EMDCYY/FFTusingFPGA/IMG_1619.jpeg

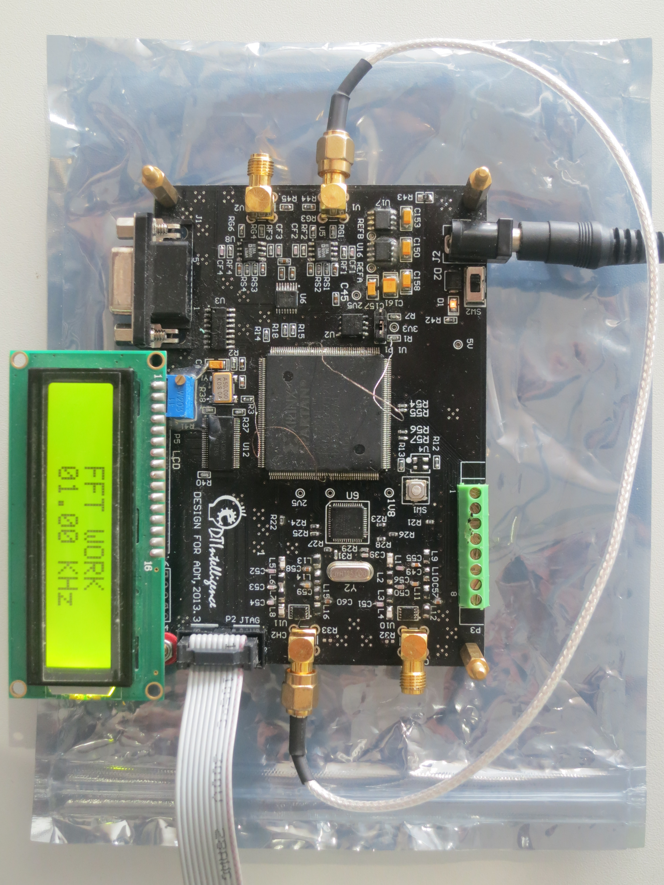
IMG_1619.jpeg
