EMDCYY/FFTusingFPGA/code/ipcore_dir/AAD.v

////////////////////////////////////////////////////////////////////////////////
// Copyright (c) 1995-2011 Xilinx, Inc.  All rights reserved.
////////////////////////////////////////////////////////////////////////////////
//   ____  ____
//  /   /\/   /
// /___/  \  /    Vendor: Xilinx
// \   \   \/     Version: O.40d
//  \   \         Application: netgen
//  /   /         Filename: AAD.v
// /___/   /\     Timestamp: Thu Aug 15 16:29:15 2013
// \   \  /  \ 
//  \___\/\___\
//             
// Command	: -w -sim -ofmt verilog "E:/Design of Laser Tracer/8.ADM/ADMDSP_CODE/ADM3.0/ipcore_dir/tmp/_cg/AAD.ngc" "E:/Design of Laser Tracer/8.ADM/ADMDSP_CODE/ADM3.0/ipcore_dir/tmp/_cg/AAD.v" 
// Device	: 3s500epq208-4
// Input file	: E:/Design of Laser Tracer/8.ADM/ADMDSP_CODE/ADM3.0/ipcore_dir/tmp/_cg/AAD.ngc
// Output file	: E:/Design of Laser Tracer/8.ADM/ADMDSP_CODE/ADM3.0/ipcore_dir/tmp/_cg/AAD.v
// # of Modules	: 1
// Design Name	: AAD
// Xilinx        : c:\Xilinx\13.1\ISE_DS\ISE\
//             
// Purpose:    
//     This verilog netlist is a verification model and uses simulation 
//     primitives which may not represent the true implementation of the 
//     device, however the netlist is functionally correct and should not 
//     be modified. This file cannot be synthesized and should only be used 
//     with supported simulation tools.
//             
// Reference:  
//     Command Line Tools User Guide, Chapter 23 and Synthesis and Simulation Design Guide, Chapter 6
//             
////////////////////////////////////////////////////////////////////////////////

`timescale 1 ns/1 ps

module AAD (
  clk, s, a, b
)/* synthesis syn_black_box syn_noprune=1 */;
  input clk;
  output [23 : 0] s;
  input [23 : 0] a;
  input [23 : 0] b;
  
  // synthesis translate_off
  
  wire N0;
  wire [22 : 0] \U0/xst_addsub/i_baseblox.i_baseblox_addsub/no_pipelining.the_addsub/i_lut4.i_lut4_addsub/carry_simple ;
  wire [23 : 0] \U0/xst_addsub/i_baseblox.i_baseblox_addsub/no_pipelining.the_addsub/i_lut4.i_lut4_addsub/halfsum ;
  wire [24 : 1] \U0/xst_addsub/i_baseblox.i_baseblox_addsub/no_pipelining.the_addsub/i_lut4.i_lut4_addsub/i_q.i_simple.qreg/fd/output ;
  wire [23 : 0] \U0/xst_addsub/i_baseblox.i_baseblox_addsub/no_pipelining.the_addsub/i_lut4.i_lut4_addsub/sum_simple ;
  assign
    s[23] = \U0/xst_addsub/i_baseblox.i_baseblox_addsub/no_pipelining.the_addsub/i_lut4.i_lut4_addsub/i_q.i_simple.qreg/fd/output [24],
    s[22] = \U0/xst_addsub/i_baseblox.i_baseblox_addsub/no_pipelining.the_addsub/i_lut4.i_lut4_addsub/i_q.i_simple.qreg/fd/output [23],
    s[21] = \U0/xst_addsub/i_baseblox.i_baseblox_addsub/no_pipelining.the_addsub/i_lut4.i_lut4_addsub/i_q.i_simple.qreg/fd/output [22],
    s[20] = \U0/xst_addsub/i_baseblox.i_baseblox_addsub/no_pipelining.the_addsub/i_lut4.i_lut4_addsub/i_q.i_simple.qreg/fd/output [21],
    s[19] = \U0/xst_addsub/i_baseblox.i_baseblox_addsub/no_pipelining.the_addsub/i_lut4.i_lut4_addsub/i_q.i_simple.qreg/fd/output [20],
    s[18] = \U0/xst_addsub/i_baseblox.i_baseblox_addsub/no_pipelining.the_addsub/i_lut4.i_lut4_addsub/i_q.i_simple.qreg/fd/output [19],
    s[17] = \U0/xst_addsub/i_baseblox.i_baseblox_addsub/no_pipelining.the_addsub/i_lut4.i_lut4_addsub/i_q.i_simple.qreg/fd/output [18],
    s[16] = \U0/xst_addsub/i_baseblox.i_baseblox_addsub/no_pipelining.the_addsub/i_lut4.i_lut4_addsub/i_q.i_simple.qreg/fd/output [17],
    s[15] = \U0/xst_addsub/i_baseblox.i_baseblox_addsub/no_pipelining.the_addsub/i_lut4.i_lut4_addsub/i_q.i_simple.qreg/fd/output [16],
    s[14] = \U0/xst_addsub/i_baseblox.i_baseblox_addsub/no_pipelining.the_addsub/i_lut4.i_lut4_addsub/i_q.i_simple.qreg/fd/output [15],
    s[13] = \U0/xst_addsub/i_baseblox.i_baseblox_addsub/no_pipelining.the_addsub/i_lut4.i_lut4_addsub/i_q.i_simple.qreg/fd/output [14],
    s[12] = \U0/xst_addsub/i_baseblox.i_baseblox_addsub/no_pipelining.the_addsub/i_lut4.i_lut4_addsub/i_q.i_simple.qreg/fd/output [13],
    s[11] = \U0/xst_addsub/i_baseblox.i_baseblox_addsub/no_pipelining.the_addsub/i_lut4.i_lut4_addsub/i_q.i_simple.qreg/fd/output [12],
    s[10] = \U0/xst_addsub/i_baseblox.i_baseblox_addsub/no_pipelining.the_addsub/i_lut4.i_lut4_addsub/i_q.i_simple.qreg/fd/output [11],
    s[9] = \U0/xst_addsub/i_baseblox.i_baseblox_addsub/no_pipelining.the_addsub/i_lut4.i_lut4_addsub/i_q.i_simple.qreg/fd/output [10],
    s[8] = \U0/xst_addsub/i_baseblox.i_baseblox_addsub/no_pipelining.the_addsub/i_lut4.i_lut4_addsub/i_q.i_simple.qreg/fd/output [9],
    s[7] = \U0/xst_addsub/i_baseblox.i_baseblox_addsub/no_pipelining.the_addsub/i_lut4.i_lut4_addsub/i_q.i_simple.qreg/fd/output [8],
    s[6] = \U0/xst_addsub/i_baseblox.i_baseblox_addsub/no_pipelining.the_addsub/i_lut4.i_lut4_addsub/i_q.i_simple.qreg/fd/output [7],
    s[5] = \U0/xst_addsub/i_baseblox.i_baseblox_addsub/no_pipelining.the_addsub/i_lut4.i_lut4_addsub/i_q.i_simple.qreg/fd/output [6],
    s[4] = \U0/xst_addsub/i_baseblox.i_baseblox_addsub/no_pipelining.the_addsub/i_lut4.i_lut4_addsub/i_q.i_simple.qreg/fd/output [5],
    s[3] = \U0/xst_addsub/i_baseblox.i_baseblox_addsub/no_pipelining.the_addsub/i_lut4.i_lut4_addsub/i_q.i_simple.qreg/fd/output [4],
    s[2] = \U0/xst_addsub/i_baseblox.i_baseblox_addsub/no_pipelining.the_addsub/i_lut4.i_lut4_addsub/i_q.i_simple.qreg/fd/output [3],
    s[1] = \U0/xst_addsub/i_baseblox.i_baseblox_addsub/no_pipelining.the_addsub/i_lut4.i_lut4_addsub/i_q.i_simple.qreg/fd/output [2],
    s[0] = \U0/xst_addsub/i_baseblox.i_baseblox_addsub/no_pipelining.the_addsub/i_lut4.i_lut4_addsub/i_q.i_simple.qreg/fd/output [1];
  GND   XST_GND (
    .G(N0)
  );
  FD #(
    .INIT ( 1'b0 ))
  \U0/xst_addsub/i_baseblox.i_baseblox_addsub/no_pipelining.the_addsub/i_lut4.i_lut4_addsub/i_q.i_simple.qreg/fd/output_1  (
    .C(clk),
    .D(\U0/xst_addsub/i_baseblox.i_baseblox_addsub/no_pipelining.the_addsub/i_lut4.i_lut4_addsub/sum_simple [0]),
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
  );
  MUXCY   \U0/xst_addsub/i_baseblox.i_baseblox_addsub/no_pipelining.the_addsub/i_lut4.i_lut4_addsub/i_simple_model.i_gt_1.carrychaingen[2].carrymux  (
    .CI(\U0/xst_addsub/i_baseblox.i_baseblox_addsub/no_pipelining.the_addsub/i_lut4.i_lut4_addsub/carry_simple [1]),
    .DI(a[2]),
    .S(\U0/xst_addsub/i_baseblox.i_baseblox_addsub/no_pipelining.the_addsub/i_lut4.i_lut4_addsub/halfsum [2]),
    .O(\U0/xst_addsub/i_baseblox.i_baseblox_addsub/no_pipelining.the_addsub/i_lut4.i_lut4_addsub/carry_simple [2])
  );
  XORCY   \U0/xst_addsub/i_baseblox.i_baseblox_addsub/no_pipelining.the_addsub/i_lut4.i_lut4_addsub/i_simple_model.i_gt_1.carrychaingen[1].carryxor  (
    .CI(\U0/xst_addsub/i_baseblox.i_baseblox_addsub/no_pipelining.the_addsub/i_lut4.i_lut4_addsub/carry_simple [0]),
    .LI(\U0/xst_addsub/i_baseblox.i_baseblox_addsub/no_pipelining.the_addsub/i_lut4.i_lut4_addsub/halfsum [1]),
    .O(\U0/xst_addsub/i_baseblox.i_baseblox_addsub/no_pipelining.the_addsub/i_lut4.i_lut4_addsub/sum_simple [1])
  );
  MUXCY   \U0/xst_addsub/i_baseblox.i_baseblox_addsub/no_pipelining.the_addsub/i_lut4.i_lut4_addsub/i_simple_model.i_gt_1.carrychaingen[1].carrymux  (
    .CI(\U0/xst_addsub/i_baseblox.i_baseblox_addsub/no_pipelining.the_addsub/i_lut4.i_lut4_addsub/carry_simple [0]),
    .DI(a[1]),
    .S(\U0/xst_addsub/i_baseblox.i_baseblox_addsub/no_pipelining.the_addsub/i_lut4.i_lut4_addsub/halfsum [1]),
    .O(\U0/xst_addsub/i_baseblox.i_baseblox_addsub/no_pipelining.the_addsub/i_lut4.i_lut4_addsub/carry_simple [1])
  );
  XORCY   \U0/xst_addsub/i_baseblox.i_baseblox_addsub/no_pipelining.the_addsub/i_lut4.i_lut4_addsub/i_simple_model.i_gt_1.carryxortop  (
    .CI(\U0/xst_addsub/i_baseblox.i_baseblox_addsub/no_pipelining.the_addsub/i_lut4.i_lut4_addsub/carry_simple [22]),
    .LI(\U0/xst_addsub/i_baseblox.i_baseblox_addsub/no_pipelining.the_addsub/i_lut4.i_lut4_addsub/halfsum [23]),
    .O(\U0/xst_addsub/i_baseblox.i_baseblox_addsub/no_pipelining.the_addsub/i_lut4.i_lut4_addsub/sum_simple [23])
  );
  XORCY   \U0/xst_addsub/i_baseblox.i_baseblox_addsub/no_pipelining.the_addsub/i_lut4.i_lut4_addsub/i_simple_model.carryxor0  (
    .CI(N0),
    .LI(\U0/xst_addsub/i_baseblox.i_baseblox_addsub/no_pipelining.the_addsub/i_lut4.i_lut4_addsub/halfsum [0]),
    .O(\U0/xst_addsub/i_baseblox.i_baseblox_addsub/no_pipelining.the_addsub/i_lut4.i_lut4_addsub/sum_simple [0])
  );
  MUXCY   \U0/xst_addsub/i_baseblox.i_baseblox_addsub/no_pipelining.the_addsub/i_lut4.i_lut4_addsub/i_simple_model.i_need_mux.carrymux0  (
    .CI(N0),
    .DI(a[0]),
    .S(\U0/xst_addsub/i_baseblox.i_baseblox_addsub/no_pipelining.the_addsub/i_lut4.i_lut4_addsub/halfsum [0]),
    .O(\U0/xst_addsub/i_baseblox.i_baseblox_addsub/no_pipelining.the_addsub/i_lut4.i_lut4_addsub/carry_simple [0])
  );
  LUT2 #(
    .INIT ( 4'h6 ))
  \U0/xst_addsub/i_baseblox.i_baseblox_addsub/no_pipelining.the_addsub/i_lut4.i_lut4_addsub/Mxor_halfsum_Result<23>1  (
    .I0(b[23]),
    .I1(a[23]),
    .O(\U0/xst_addsub/i_baseblox.i_baseblox_addsub/no_pipelining.the_addsub/i_lut4.i_lut4_addsub/halfsum [23])
  );
  LUT2 #(
    .INIT ( 4'h6 ))
  \U0/xst_addsub/i_baseblox.i_baseblox_addsub/no_pipelining.the_addsub/i_lut4.i_lut4_addsub/Mxor_halfsum_Result<22>1  (
    .I0(b[22]),
    .I1(a[22]),
    .O(\U0/xst_addsub/i_baseblox.i_baseblox_addsub/no_pipelining.the_addsub/i_lut4.i_lut4_addsub/halfsum [22])
  );
  LUT2 #(
    .INIT ( 4'h6 ))
  \U0/xst_addsub/i_baseblox.i_baseblox_addsub/no_pipelining.the_addsub/i_lut4.i_lut4_addsub/Mxor_halfsum_Result<21>1  (
    .I0(b[21]),
    .I1(a[21]),
    .O(\U0/xst_addsub/i_baseblox.i_baseblox_addsub/no_pipelining.the_addsub/i_lut4.i_lut4_addsub/halfsum [21])
  );
  LUT2 #(
    .INIT ( 4'h6 ))
  \U0/xst_addsub/i_baseblox.i_baseblox_addsub/no_pipelining.the_addsub/i_lut4.i_lut4_addsub/Mxor_halfsum_Result<20>1  (
    .I0(b[20]),
    .I1(a[20]),
    .O(\U0/xst_addsub/i_baseblox.i_baseblox_addsub/no_pipelining.the_addsub/i_lut4.i_lut4_addsub/halfsum [20])
  );
  LUT2 #(
    .INIT ( 4'h6 ))
  \U0/xst_addsub/i_baseblox.i_baseblox_addsub/no_pipelining.the_addsub/i_lut4.i_lut4_addsub/Mxor_halfsum_Result<19>1  (
    .I0(b[19]),
    .I1(a[19]),
    .O(\U0/xst_addsub/i_baseblox.i_baseblox_addsub/no_pipelining.the_addsub/i_lut4.i_lut4_addsub/halfsum [19])
  );
  LUT2 #(
    .INIT ( 4'h6 ))
  \U0/xst_addsub/i_baseblox.i_baseblox_addsub/no_pipelining.the_addsub/i_lut4.i_lut4_addsub/Mxor_halfsum_Result<18>1  (
    .I0(b[18]),
    .I1(a[18]),
    .O(\U0/xst_addsub/i_baseblox.i_baseblox_addsub/no_pipelining.the_addsub/i_lut4.i_lut4_addsub/halfsum [18])
  );
  LUT2 #(
    .INIT ( 4'h6 ))
  \U0/xst_addsub/i_baseblox.i_baseblox_addsub/no_pipelining.the_addsub/i_lut4.i_lut4_addsub/Mxor_halfsum_Result<17>1  (
    .I0(b[17]),
    .I1(a[17]),
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
    .O(\U0/xst_addsub/i_baseblox.i_baseblox_addsub/no_pipelining.the_addsub/i_lut4.i_lut4_addsub/halfsum [3])
  );
  LUT2 #(
    .INIT ( 4'h6 ))
  \U0/xst_addsub/i_baseblox.i_baseblox_addsub/no_pipelining.the_addsub/i_lut4.i_lut4_addsub/Mxor_halfsum_Result<2>1  (
    .I0(b[2]),
    .I1(a[2]),
    .O(\U0/xst_addsub/i_baseblox.i_baseblox_addsub/no_pipelining.the_addsub/i_lut4.i_lut4_addsub/halfsum [2])
  );
  LUT2 #(
    .INIT ( 4'h6 ))
  \U0/xst_addsub/i_baseblox.i_baseblox_addsub/no_pipelining.the_addsub/i_lut4.i_lut4_addsub/Mxor_halfsum_Result<1>1  (
    .I0(b[1]),
    .I1(a[1]),
    .O(\U0/xst_addsub/i_baseblox.i_baseblox_addsub/no_pipelining.the_addsub/i_lut4.i_lut4_addsub/halfsum [1])
  );
  LUT2 #(
    .INIT ( 4'h6 ))
  \U0/xst_addsub/i_baseblox.i_baseblox_addsub/no_pipelining.the_addsub/i_lut4.i_lut4_addsub/Mxor_halfsum_Result<0>1  (
    .I0(b[0]),
    .I1(a[0]),
    .O(\U0/xst_addsub/i_baseblox.i_baseblox_addsub/no_pipelining.the_addsub/i_lut4.i_lut4_addsub/halfsum [0])
  );

// synthesis translate_on

endmodule

// synthesis translate_off

`ifndef GLBL
`define GLBL

`timescale  1 ps / 1 ps

module glbl ();

    parameter ROC_WIDTH = 100000;
    parameter TOC_WIDTH = 0;

//--------   STARTUP Globals --------------
    wire GSR;
    wire GTS;
    wire GWE;
    wire PRLD;
    tri1 p_up_tmp;
    tri (weak1, strong0) PLL_LOCKG = p_up_tmp;

    wire PROGB_GLBL;

    reg GSR_int;
    reg GTS_int;
    reg PRLD_int;

//--------   JTAG Globals --------------
    wire JTAG_TDO_GLBL;
    wire JTAG_TCK_GLBL;
    wire JTAG_TDI_GLBL;
    wire JTAG_TMS_GLBL;
    wire JTAG_TRST_GLBL;

    reg JTAG_CAPTURE_GLBL;
    reg JTAG_RESET_GLBL;
    reg JTAG_SHIFT_GLBL;
    reg JTAG_UPDATE_GLBL;
    reg JTAG_RUNTEST_GLBL;

    reg JTAG_SEL1_GLBL = 0;
    reg JTAG_SEL2_GLBL = 0 ;
    reg JTAG_SEL3_GLBL = 0;
    reg JTAG_SEL4_GLBL = 0;

    reg JTAG_USER_TDO1_GLBL = 1'bz;
    reg JTAG_USER_TDO2_GLBL = 1'bz;
    reg JTAG_USER_TDO3_GLBL = 1'bz;
    reg JTAG_USER_TDO4_GLBL = 1'bz;

    assign (weak1, weak0) GSR = GSR_int;
    assign (weak1, weak0) GTS = GTS_int;
    assign (weak1, weak0) PRLD = PRLD_int;

    initial begin
	GSR_int = 1'b1;
	PRLD_int = 1'b1;
	#(ROC_WIDTH)
	GSR_int = 1'b0;
	PRLD_int = 1'b0;
    end

    initial begin
	GTS_int = 1'b1;
	#(TOC_WIDTH)
	GTS_int = 1'b0;
    end

endmodule

`endif

// synthesis translate_on
