EMDCYY/FFTusingFPGA/code/ipcore_dir/ARCTAN.v

////////////////////////////////////////////////////////////////////////////////
// Copyright (c) 1995-2011 Xilinx, Inc.  All rights reserved.
////////////////////////////////////////////////////////////////////////////////
//   ____  ____
//  /   /\/   /
// /___/  \  /    Vendor: Xilinx
// \   \   \/     Version: O.40d
//  \   \         Application: netgen
//  /   /         Filename: ARCTAN.v
// /___/   /\     Timestamp: Tue May 28 14:38:06 2013
// \   \  /  \ 
//  \___\/\___\
//             
// Command	: -intstyle ise -w -sim -ofmt verilog ./tmp/_cg\ARCTAN.ngc ./tmp/_cg\ARCTAN.v 
// Device	: 3s500epq208-4
// Input file	: ./tmp/_cg/ARCTAN.ngc
// Output file	: ./tmp/_cg/ARCTAN.v
// # of Modules	: 1
// Design Name	: ARCTAN
// Xilinx        : c:\Xilinx\13.1\ISE_DS\ISE\
//             
// Purpose:    
//     This verilog netlist is a verification model and uses simulation 
//     primitives which may not represent the true implementation of the 
//     device, however the netlist is functionally correct and should not 
//     be modified. This file cannot be synthesized and should only be used 
//     with supported simulation tools.
//             
// Reference:  
//     Command Line Tools User Guide, Chapter 23 and Synthesis and Simulation Design Guide, Chapter 6
//             
////////////////////////////////////////////////////////////////////////////////

`timescale 1 ns/1 ps

module ARCTAN (
  sclr, clk, y_in, phase_out, x_in
)/* synthesis syn_black_box syn_noprune=1 */;
  input sclr;
  input clk;
  input [11 : 0] y_in;
  output [11 : 0] phase_out;
  input [11 : 0] x_in;
  
  // synthesis translate_off
  
  wire \blk00000003/sig00000927 ;
  wire \blk00000003/sig00000926 ;
  wire \blk00000003/sig00000925 ;
  wire \blk00000003/sig00000924 ;
  wire \blk00000003/sig00000923 ;
  wire \blk00000003/sig00000922 ;
  wire \blk00000003/sig00000921 ;
  wire \blk00000003/sig00000920 ;
  wire \blk00000003/sig0000091f ;
  wire \blk00000003/sig0000091e ;
  wire \blk00000003/sig0000091d ;
  wire \blk00000003/sig0000091c ;
  wire \blk00000003/sig0000091b ;
  wire \blk00000003/sig0000091a ;
  wire \blk00000003/sig00000919 ;
  wire \blk00000003/sig00000918 ;
  wire \blk00000003/sig00000917 ;
  wire \blk00000003/sig00000916 ;
  wire \blk00000003/sig00000915 ;
  wire \blk00000003/sig00000914 ;
  wire \blk00000003/sig00000913 ;
  wire \blk00000003/sig00000912 ;
  wire \blk00000003/sig00000911 ;
  wire \blk00000003/sig00000910 ;
  wire \blk00000003/sig0000090f ;
  wire \blk00000003/sig0000090e ;
  wire \blk00000003/sig0000090d ;
  wire \blk00000003/sig0000090c ;
  wire \blk00000003/sig0000090b ;
  wire \blk00000003/sig0000090a ;
  wire \blk00000003/sig00000909 ;
  wire \blk00000003/sig00000908 ;
  wire \blk00000003/sig00000907 ;
  wire \blk00000003/sig00000906 ;
  wire \blk00000003/sig00000905 ;
  wire \blk00000003/sig00000904 ;
  wire \blk00000003/sig00000903 ;
  wire \blk00000003/sig00000902 ;
  wire \blk00000003/sig00000901 ;
  wire \blk00000003/sig00000900 ;
  wire \blk00000003/sig000008ff ;
  wire \blk00000003/sig000008fe ;
  wire \blk00000003/sig000008fd ;
  wire \blk00000003/sig000008fc ;
  wire \blk00000003/sig000008fb ;
  wire \blk00000003/sig000008fa ;
  wire \blk00000003/sig000008f9 ;
  wire \blk00000003/sig000008f8 ;
  wire \blk00000003/sig000008f7 ;
  wire \blk00000003/sig000008f6 ;
  wire \blk00000003/sig000008f5 ;
  wire \blk00000003/sig000008f4 ;
  wire \blk00000003/sig000008f3 ;
  wire \blk00000003/sig000008f2 ;
  wire \blk00000003/sig000008f1 ;
  wire \blk00000003/sig000008f0 ;
  wire \blk00000003/sig000008ef ;
  wire \blk00000003/sig000008ee ;
  wire \blk00000003/sig000008ed ;
  wire \blk00000003/sig000008ec ;
  wire \blk00000003/sig000008eb ;
  wire \blk00000003/sig000008ea ;
  wire \blk00000003/sig000008e9 ;
  wire \blk00000003/sig000008e8 ;
  wire \blk00000003/sig000008e7 ;
  wire \blk00000003/sig000008e6 ;
  wire \blk00000003/sig000008e5 ;
  wire \blk00000003/sig000008e4 ;
  wire \blk00000003/sig000008e3 ;
  wire \blk00000003/sig000008e2 ;
  wire \blk00000003/sig000008e1 ;
  wire \blk00000003/sig000008e0 ;
  wire \blk00000003/sig000008df ;
  wire \blk00000003/sig000008de ;
  wire \blk00000003/sig000008dd ;
  wire \blk00000003/sig000008dc ;
  wire \blk00000003/sig000008db ;
  wire \blk00000003/sig000008da ;
  wire \blk00000003/sig000008d9 ;
  wire \blk00000003/sig000008d8 ;
  wire \blk00000003/sig000008d7 ;
  wire \blk00000003/sig000008d6 ;
  wire \blk00000003/sig000008d5 ;
  wire \blk00000003/sig000008d4 ;
  wire \blk00000003/sig000008d3 ;
  wire \blk00000003/sig000008d2 ;
  wire \blk00000003/sig000008d1 ;
  wire \blk00000003/sig000008d0 ;
  wire \blk00000003/sig000008cf ;
  wire \blk00000003/sig000008ce ;
  wire \blk00000003/sig000008cd ;
  wire \blk00000003/sig000008cc ;
  wire \blk00000003/sig000008cb ;
  wire \blk00000003/sig000008ca ;
  wire \blk00000003/sig000008c9 ;
  wire \blk00000003/sig000008c8 ;
  wire \blk00000003/sig000008c7 ;
  wire \blk00000003/sig000008c6 ;
  wire \blk00000003/sig000008c5 ;
  wire \blk00000003/sig000008c4 ;
  wire \blk00000003/sig000008c3 ;
  wire \blk00000003/sig000008c2 ;
  wire \blk00000003/sig000008c1 ;
  wire \blk00000003/sig000008c0 ;
  wire \blk00000003/sig000008bf ;
  wire \blk00000003/sig000008be ;
  wire \blk00000003/sig000008bd ;
  wire \blk00000003/sig000008bc ;
  wire \blk00000003/sig000008bb ;
  wire \blk00000003/sig000008ba ;
  wire \blk00000003/sig000008b9 ;
  wire \blk00000003/sig000008b8 ;
  wire \blk00000003/sig000008b7 ;
  wire \blk00000003/sig000008b6 ;
  wire \blk00000003/sig000008b5 ;
  wire \blk00000003/sig000008b4 ;
  wire \blk00000003/sig000008b3 ;
  wire \blk00000003/sig000008b2 ;
  wire \blk00000003/sig000008b1 ;
  wire \blk00000003/sig000008b0 ;
  wire \blk00000003/sig000008af ;
  wire \blk00000003/sig000008ae ;
  wire \blk00000003/sig000008ad ;
  wire \blk00000003/sig000008ac ;
  wire \blk00000003/sig000008ab ;
  wire \blk00000003/sig000008aa ;
  wire \blk00000003/sig000008a9 ;
  wire \blk00000003/sig000008a8 ;
  wire \blk00000003/sig000008a7 ;
  wire \blk00000003/sig000008a6 ;
  wire \blk00000003/sig000008a5 ;
  wire \blk00000003/sig000008a4 ;
  wire \blk00000003/sig000008a3 ;
  wire \blk00000003/sig000008a2 ;
  wire \blk00000003/sig000008a1 ;
  wire \blk00000003/sig000008a0 ;
  wire \blk00000003/sig0000089f ;
  wire \blk00000003/sig0000089e ;
  wire \blk00000003/sig0000089d ;
  wire \blk00000003/sig0000089c ;
  wire \blk00000003/sig0000089b ;
  wire \blk00000003/sig0000089a ;
  wire \blk00000003/sig00000899 ;
  wire \blk00000003/sig00000898 ;
  wire \blk00000003/sig00000897 ;
  wire \blk00000003/sig00000896 ;
  wire \blk00000003/sig00000895 ;
  wire \blk00000003/sig00000894 ;
  wire \blk00000003/sig00000893 ;
  wire \blk00000003/sig00000892 ;
  wire \blk00000003/sig00000891 ;
  wire \blk00000003/sig00000890 ;
  wire \blk00000003/sig0000088f ;
  wire \blk00000003/sig0000088e ;
  wire \blk00000003/sig0000088d ;
  wire \blk00000003/sig0000088c ;
  wire \blk00000003/sig0000088b ;
  wire \blk00000003/sig0000088a ;
  wire \blk00000003/sig00000889 ;
  wire \blk00000003/sig00000888 ;
  wire \blk00000003/sig00000887 ;
  wire \blk00000003/sig00000886 ;
  wire \blk00000003/sig00000885 ;
  wire \blk00000003/sig00000884 ;
  wire \blk00000003/sig00000883 ;
  wire \blk00000003/sig00000882 ;
  wire \blk00000003/sig00000881 ;
  wire \blk00000003/sig00000880 ;
  wire \blk00000003/sig0000087f ;
  wire \blk00000003/sig0000087e ;
  wire \blk00000003/sig0000087d ;
  wire \blk00000003/sig0000087c ;
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
  wire \NLW_blk00000003/blk000000e7_O_UNCONNECTED ;
  wire \NLW_blk00000003/blk000000e6_O_UNCONNECTED ;
  wire \NLW_blk00000003/blk000000c5_O_UNCONNECTED ;
  wire \NLW_blk00000003/blk000000c3_O_UNCONNECTED ;
  wire \NLW_blk00000003/blk000000c1_O_UNCONNECTED ;
  wire \NLW_blk00000003/blk000000bf_O_UNCONNECTED ;
  wire \NLW_blk00000003/blk000000bd_O_UNCONNECTED ;
  wire \NLW_blk00000003/blk000000bb_O_UNCONNECTED ;
  wire \NLW_blk00000003/blk000000b9_O_UNCONNECTED ;
  wire \NLW_blk00000003/blk000000b7_O_UNCONNECTED ;
  wire \NLW_blk00000003/blk000000b5_O_UNCONNECTED ;
  wire \NLW_blk00000003/blk000000b3_O_UNCONNECTED ;
  wire \NLW_blk00000003/blk000000b1_O_UNCONNECTED ;
  wire \NLW_blk00000003/blk000000af_O_UNCONNECTED ;
  wire \NLW_blk00000003/blk000000ad_O_UNCONNECTED ;
  wire \NLW_blk00000003/blk000000ab_O_UNCONNECTED ;
  wire \NLW_blk00000003/blk000000a9_O_UNCONNECTED ;
  wire \NLW_blk00000003/blk000000a7_O_UNCONNECTED ;
  wire \NLW_blk00000003/blk000000a6_O_UNCONNECTED ;
  wire \NLW_blk00000003/blk000000a2_O_UNCONNECTED ;
  wire \NLW_blk00000003/blk000000a0_O_UNCONNECTED ;
  wire \NLW_blk00000003/blk0000009e_O_UNCONNECTED ;
  wire \NLW_blk00000003/blk0000009c_O_UNCONNECTED ;
  wire \NLW_blk00000003/blk0000009a_O_UNCONNECTED ;
  wire \NLW_blk00000003/blk00000098_O_UNCONNECTED ;
  wire \NLW_blk00000003/blk00000096_O_UNCONNECTED ;
  wire \NLW_blk00000003/blk00000094_O_UNCONNECTED ;
  wire \NLW_blk00000003/blk00000092_O_UNCONNECTED ;
  wire \NLW_blk00000003/blk00000090_O_UNCONNECTED ;
  wire \NLW_blk00000003/blk0000008e_O_UNCONNECTED ;
  wire \NLW_blk00000003/blk0000008c_O_UNCONNECTED ;
  wire \NLW_blk00000003/blk0000008a_O_UNCONNECTED ;
  wire \NLW_blk00000003/blk00000088_O_UNCONNECTED ;
  wire \NLW_blk00000003/blk00000086_O_UNCONNECTED ;
  wire \NLW_blk00000003/blk00000084_O_UNCONNECTED ;
  wire \NLW_blk00000003/blk00000083_O_UNCONNECTED ;
  wire \NLW_blk00000003/blk00000039_O_UNCONNECTED ;
  wire \NLW_blk00000003/blk00000008_O_UNCONNECTED ;
  wire [11 : 0] x_in_0;
  wire [11 : 0] y_in_1;
  wire [11 : 0] phase_out_2;
  assign
    y_in_1[11] = y_in[11],
    y_in_1[10] = y_in[10],
    y_in_1[9] = y_in[9],
    y_in_1[8] = y_in[8],
    y_in_1[7] = y_in[7],
    y_in_1[6] = y_in[6],
    y_in_1[5] = y_in[5],
    y_in_1[4] = y_in[4],
    y_in_1[3] = y_in[3],
    y_in_1[2] = y_in[2],
    y_in_1[1] = y_in[1],
    y_in_1[0] = y_in[0],
    phase_out[11] = phase_out_2[11],
    phase_out[10] = phase_out_2[10],
    phase_out[9] = phase_out_2[9],
    phase_out[8] = phase_out_2[8],
    phase_out[7] = phase_out_2[7],
    phase_out[6] = phase_out_2[6],
    phase_out[5] = phase_out_2[5],
    phase_out[4] = phase_out_2[4],
    phase_out[3] = phase_out_2[3],
    phase_out[2] = phase_out_2[2],
    phase_out[1] = phase_out_2[1],
    phase_out[0] = phase_out_2[0],
    x_in_0[11] = x_in[11],
    x_in_0[10] = x_in[10],
    x_in_0[9] = x_in[9],
    x_in_0[8] = x_in[8],
    x_in_0[7] = x_in[7],
    x_in_0[6] = x_in[6],
    x_in_0[5] = x_in[5],
    x_in_0[4] = x_in[4],
    x_in_0[3] = x_in[3],
    x_in_0[2] = x_in[2],
    x_in_0[1] = x_in[1],
    x_in_0[0] = x_in[0];
  VCC   blk00000001 (
    .P(NLW_blk00000001_P_UNCONNECTED)
  );
  GND   blk00000002 (
    .G(NLW_blk00000002_G_UNCONNECTED)
  );
  FDRE #(
    .INIT ( 1'b0 ))
  \blk00000003/blk00000977  (
    .C(clk),
    .CE(\blk00000003/sig00000028 ),
    .D(\blk00000003/sig00000927 ),
    .R(sclr),
    .Q(\blk00000003/sig00000912 )
  );
  LUT2 #(
    .INIT ( 4'h8 ))
  \blk00000003/blk00000976  (
    .I0(\blk00000003/sig0000091c ),
    .I1(\blk00000003/sig00000925 ),
    .O(\blk00000003/sig00000927 )
  );
  FDRE #(
    .INIT ( 1'b0 ))
  \blk00000003/blk00000975  (
    .C(clk),
    .CE(\blk00000003/sig00000028 ),
    .D(\blk00000003/sig00000926 ),
    .R(sclr),
    .Q(\blk00000003/sig00000913 )
  );
  LUT2 #(
    .INIT ( 4'h8 ))
  \blk00000003/blk00000974  (
    .I0(\blk00000003/sig0000091a ),
    .I1(\blk00000003/sig00000925 ),
    .O(\blk00000003/sig00000926 )
  );
  FDRE   \blk00000003/blk00000973  (
    .C(clk),
    .CE(\blk00000003/sig00000028 ),
    .D(\blk00000003/sig00000924 ),
    .R(sclr),
    .Q(\blk00000003/sig00000925 )
  );
  FDRE   \blk00000003/blk00000972  (
    .C(clk),
    .CE(\blk00000003/sig00000028 ),
    .D(\blk00000003/sig00000923 ),
    .R(sclr),
    .Q(\blk00000003/sig00000924 )
  );
  FDRE   \blk00000003/blk00000971  (
    .C(clk),
    .CE(\blk00000003/sig00000028 ),
    .D(\blk00000003/sig00000922 ),
    .R(sclr),
    .Q(\blk00000003/sig00000923 )
  );
  FDRE   \blk00000003/blk00000970  (
    .C(clk),
    .CE(\blk00000003/sig00000028 ),
    .D(\blk00000003/sig00000921 ),
    .R(sclr),
    .Q(\blk00000003/sig00000922 )
  );
  FDRE   \blk00000003/blk0000096f  (
    .C(clk),
    .CE(\blk00000003/sig00000028 ),
    .D(\blk00000003/sig00000920 ),
    .R(sclr),
    .Q(\blk00000003/sig00000921 )
  );
  FDRE   \blk00000003/blk0000096e  (
    .C(clk),
    .CE(\blk00000003/sig00000028 ),
    .D(\blk00000003/sig0000091f ),
    .R(sclr),
    .Q(\blk00000003/sig00000920 )
  );
  FDRE   \blk00000003/blk0000096d  (
    .C(clk),
    .CE(\blk00000003/sig00000028 ),
    .D(\blk00000003/sig0000091e ),
    .R(sclr),
    .Q(\blk00000003/sig0000091f )
  );
  FDRE   \blk00000003/blk0000096c  (
    .C(clk),
    .CE(\blk00000003/sig00000028 ),
    .D(\blk00000003/sig0000091d ),
    .R(sclr),
    .Q(\blk00000003/sig0000091e )
  );
  FDRE   \blk00000003/blk0000096b  (
    .C(clk),
    .CE(\blk00000003/sig00000028 ),
    .D(\blk00000003/sig00000028 ),
    .R(sclr),
    .Q(\blk00000003/sig0000091d )
  );
  FDE #(
    .INIT ( 1'b0 ))
  \blk00000003/blk0000096a  (
    .C(clk),
    .CE(\blk00000003/sig00000028 ),
    .D(\blk00000003/sig0000091b ),
    .Q(\blk00000003/sig0000091c )
  );
  SRL16E #(
    .INIT ( 16'h0000 ))
  \blk00000003/blk00000969  (
    .A0(\blk00000003/sig00000028 ),
    .A1(\blk00000003/sig00000028 ),
    .A2(\blk00000003/sig00000028 ),
    .A3(\blk00000003/sig00000002 ),
    .CE(\blk00000003/sig00000028 ),
    .CLK(clk),
    .D(\blk00000003/sig00000125 ),
    .Q(\blk00000003/sig0000091b )
  );
  FDE #(
    .INIT ( 1'b0 ))
  \blk00000003/blk00000968  (
    .C(clk),
    .CE(\blk00000003/sig00000028 ),
    .D(\blk00000003/sig00000919 ),
    .Q(\blk00000003/sig0000091a )
  );
  SRL16E #(
    .INIT ( 16'h0000 ))
  \blk00000003/blk00000967  (
    .A0(\blk00000003/sig00000028 ),
    .A1(\blk00000003/sig00000028 ),
    .A2(\blk00000003/sig00000028 ),
    .A3(\blk00000003/sig00000002 ),
    .CE(\blk00000003/sig00000028 ),
    .CLK(clk),
    .D(\blk00000003/sig00000123 ),
    .Q(\blk00000003/sig00000919 )
  );
  INV   \blk00000003/blk00000966  (
    .I(\blk00000003/sig0000005c ),
    .O(\blk00000003/sig000001ad )
  );
  INV   \blk00000003/blk00000965  (
    .I(\blk00000003/sig0000005c ),
    .O(\blk00000003/sig000001aa )
  );
  INV   \blk00000003/blk00000964  (
    .I(\blk00000003/sig0000005c ),
    .O(\blk00000003/sig000001a4 )
  );
  INV   \blk00000003/blk00000963  (
    .I(\blk00000003/sig0000005c ),
    .O(\blk00000003/sig000001a1 )
  );
  INV   \blk00000003/blk00000962  (
    .I(\blk00000003/sig0000005c ),
    .O(\blk00000003/sig0000019b )
  );
  INV   \blk00000003/blk00000961  (
    .I(\blk00000003/sig0000005c ),
    .O(\blk00000003/sig00000195 )
  );
  INV   \blk00000003/blk00000960  (
    .I(\blk00000003/sig0000005c ),
    .O(\blk00000003/sig00000192 )
  );
  INV   \blk00000003/blk0000095f  (
    .I(\blk00000003/sig0000005c ),
    .O(\blk00000003/sig000001b0 )
  );
  INV   \blk00000003/blk0000095e  (
    .I(\blk00000003/sig0000005c ),
    .O(\blk00000003/sig000001ce )
  );
  INV   \blk00000003/blk0000095d  (
    .I(\blk00000003/sig00000188 ),
    .O(\blk00000003/sig00000126 )
  );
  INV   \blk00000003/blk0000095c  (
    .I(\blk00000003/sig0000009f ),
    .O(\blk00000003/sig000001fe )
  );
  INV   \blk00000003/blk0000095b  (
    .I(\blk00000003/sig0000006e ),
    .O(\blk00000003/sig00000122 )
  );
  INV   \blk00000003/blk0000095a  (
    .I(\blk00000003/sig0000002b ),
    .O(\blk00000003/sig00000124 )
  );
  INV   \blk00000003/blk00000959  (
    .I(\blk00000003/sig0000009f ),
    .O(\blk00000003/sig000001d3 )
  );
  LUT3 #(
    .INIT ( 8'h4E ))
  \blk00000003/blk00000958  (
    .I0(\blk00000003/sig00000916 ),
    .I1(\blk00000003/sig00000622 ),
    .I2(\blk00000003/sig000004d9 ),
    .O(\blk00000003/sig0000056e )
  );
  LUT3 #(
    .INIT ( 8'h4E ))
  \blk00000003/blk00000957  (
    .I0(\blk00000003/sig00000917 ),
    .I1(\blk00000003/sig00000494 ),
    .I2(\blk00000003/sig0000034b ),
    .O(\blk00000003/sig000003e0 )
  );
  FDR #(
    .INIT ( 1'b0 ))
  \blk00000003/blk00000956  (
    .C(clk),
    .D(\blk00000003/sig000001ff ),
    .R(sclr),
    .Q(\blk00000003/sig00000281 )
  );
  FDR #(
    .INIT ( 1'b0 ))
  \blk00000003/blk00000955  (
    .C(clk),
    .D(\blk00000003/sig00000308 ),
    .R(sclr),
    .Q(\blk00000003/sig000003cd )
  );
  FDR #(
    .INIT ( 1'b0 ))
  \blk00000003/blk00000954  (
    .C(clk),
    .D(\blk00000003/sig000001bd ),
    .R(sclr),
    .Q(\blk00000003/sig00000306 )
  );
  FDR #(
    .INIT ( 1'b0 ))
  \blk00000003/blk00000953  (
    .C(clk),
    .D(\blk00000003/sig00000496 ),
    .R(sclr),
    .Q(\blk00000003/sig0000055b )
  );
  FDR #(
    .INIT ( 1'b0 ))
  \blk00000003/blk00000952  (
    .C(clk),
    .D(\blk00000003/sig000003cf ),
    .R(sclr),
    .Q(\blk00000003/sig00000494 )
  );
  FDRE #(
    .INIT ( 1'b0 ))
  \blk00000003/blk00000951  (
    .C(clk),
    .CE(\blk00000003/sig00000028 ),
    .D(\blk00000003/sig00000028 ),
    .R(sclr),
    .Q(\blk00000003/sig00000918 )
  );
  FDR #(
    .INIT ( 1'b0 ))
  \blk00000003/blk00000950  (
    .C(clk),
    .D(\blk00000003/sig00000624 ),
    .R(sclr),
    .Q(\blk00000003/sig000006e9 )
  );
  FDR #(
    .INIT ( 1'b0 ))
  \blk00000003/blk0000094f  (
    .C(clk),
    .D(\blk00000003/sig0000055d ),
    .R(sclr),
    .Q(\blk00000003/sig00000622 )
  );
  FDRE #(
    .INIT ( 1'b0 ))
  \blk00000003/blk0000094e  (
    .C(clk),
    .CE(\blk00000003/sig00000028 ),
    .D(\blk00000003/sig0000090e ),
    .R(sclr),
    .Q(\blk00000003/sig00000917 )
  );
  FDR #(
    .INIT ( 1'b0 ))
  \blk00000003/blk0000094d  (
    .C(clk),
    .D(\blk00000003/sig000007b2 ),
    .R(sclr),
    .Q(\blk00000003/sig00000877 )
  );
  FDR #(
    .INIT ( 1'b0 ))
  \blk00000003/blk0000094c  (
    .C(clk),
    .D(\blk00000003/sig000006eb ),
    .R(sclr),
    .Q(\blk00000003/sig000007b0 )
  );
  FDRE #(
    .INIT ( 1'b0 ))
  \blk00000003/blk0000094b  (
    .C(clk),
    .CE(\blk00000003/sig00000028 ),
    .D(\blk00000003/sig0000090a ),
    .R(sclr),
    .Q(\blk00000003/sig00000916 )
  );
  LUT4 #(
    .INIT ( 16'h53CA ))
  \blk00000003/blk0000094a  (
    .I0(\blk00000003/sig0000006e ),
    .I1(\blk00000003/sig0000002b ),
    .I2(\blk00000003/sig000000e0 ),
    .I3(\blk00000003/sig000000c8 ),
    .O(\blk00000003/sig00000072 )
  );
  LUT4 #(
    .INIT ( 16'h53CA ))
  \blk00000003/blk00000949  (
    .I0(\blk00000003/sig0000002b ),
    .I1(\blk00000003/sig0000006e ),
    .I2(\blk00000003/sig000000c8 ),
    .I3(\blk00000003/sig000000e0 ),
    .O(\blk00000003/sig0000002f )
  );
  LUT2 #(
    .INIT ( 4'h6 ))
  \blk00000003/blk00000948  (
    .I0(\blk00000003/sig000000df ),
    .I1(\blk00000003/sig000000c7 ),
    .O(\blk00000003/sig000000e3 )
  );
  LUT3 #(
    .INIT ( 8'hB1 ))
  \blk00000003/blk00000947  (
    .I0(\blk00000003/sig00000902 ),
    .I1(\blk00000003/sig0000087a ),
    .I2(\blk00000003/sig000007f5 ),
    .O(\blk00000003/sig000008ac )
  );
  LUT4 #(
    .INIT ( 16'hAA69 ))
  \blk00000003/blk00000946  (
    .I0(\blk00000003/sig00000241 ),
    .I1(\blk00000003/sig00000200 ),
    .I2(\blk00000003/sig000001be ),
    .I3(\blk00000003/sig00000910 ),
    .O(\blk00000003/sig00000299 )
  );
  LUT4 #(
    .INIT ( 16'h21DE ))
  \blk00000003/blk00000945  (
    .I0(\blk00000003/sig00000200 ),
    .I1(\blk00000003/sig00000910 ),
    .I2(\blk00000003/sig000001be ),
    .I3(\blk00000003/sig00000241 ),
    .O(\blk00000003/sig00000256 )
  );
  LUT4 #(
    .INIT ( 16'hAA69 ))
  \blk00000003/blk00000944  (
    .I0(\blk00000003/sig000002c6 ),
    .I1(\blk00000003/sig00000284 ),
    .I2(\blk00000003/sig00000309 ),
    .I3(\blk00000003/sig0000090e ),
    .O(\blk00000003/sig00000360 )
  );
  LUT4 #(
    .INIT ( 16'h21DE ))
  \blk00000003/blk00000943  (
    .I0(\blk00000003/sig00000284 ),
    .I1(\blk00000003/sig0000090e ),
    .I2(\blk00000003/sig00000309 ),
    .I3(\blk00000003/sig000002c6 ),
    .O(\blk00000003/sig0000031e )
  );
  LUT4 #(
    .INIT ( 16'hAA69 ))
  \blk00000003/blk00000942  (
    .I0(\blk00000003/sig0000038d ),
    .I1(\blk00000003/sig0000034b ),
    .I2(\blk00000003/sig000003d0 ),
    .I3(\blk00000003/sig0000090c ),
    .O(\blk00000003/sig00000427 )
  );
  LUT4 #(
    .INIT ( 16'h21DE ))
  \blk00000003/blk00000941  (
    .I0(\blk00000003/sig0000034b ),
    .I1(\blk00000003/sig0000090c ),
    .I2(\blk00000003/sig000003d0 ),
    .I3(\blk00000003/sig0000038d ),
    .O(\blk00000003/sig000003e5 )
  );
  LUT4 #(
    .INIT ( 16'hAA69 ))
  \blk00000003/blk00000940  (
    .I0(\blk00000003/sig00000454 ),
    .I1(\blk00000003/sig00000412 ),
    .I2(\blk00000003/sig00000497 ),
    .I3(\blk00000003/sig0000090a ),
    .O(\blk00000003/sig000004ee )
  );
  LUT4 #(
    .INIT ( 16'h21DE ))
  \blk00000003/blk0000093f  (
    .I0(\blk00000003/sig00000412 ),
    .I1(\blk00000003/sig0000090a ),
    .I2(\blk00000003/sig00000497 ),
    .I3(\blk00000003/sig00000454 ),
    .O(\blk00000003/sig000004ac )
  );
  LUT4 #(
    .INIT ( 16'hAA69 ))
  \blk00000003/blk0000093e  (
    .I0(\blk00000003/sig0000051b ),
    .I1(\blk00000003/sig000004d9 ),
    .I2(\blk00000003/sig0000055e ),
    .I3(\blk00000003/sig00000908 ),
    .O(\blk00000003/sig000005b5 )
  );
  LUT4 #(
    .INIT ( 16'h21DE ))
  \blk00000003/blk0000093d  (
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
    .I1(\blk00000003/sig000007f5 ),
    .I2(\blk00000003/sig0000087a ),
    .I3(\blk00000003/sig00000902 ),
    .O(\blk00000003/sig000008bf )
  );
  LUT4 #(
    .INIT ( 16'hAA69 ))
  \blk00000003/blk0000092b  (
    .I0(\blk00000003/sig0000083d ),
    .I1(\blk00000003/sig000007f5 ),
    .I2(\blk00000003/sig0000087a ),
    .I3(\blk00000003/sig00000902 ),
    .O(\blk00000003/sig000008c1 )
  );
  LUT4 #(
    .INIT ( 16'h21DE ))
  \blk00000003/blk0000092a  (
    .I0(\blk00000003/sig000007f5 ),
    .I1(\blk00000003/sig00000902 ),
    .I2(\blk00000003/sig0000087a ),
    .I3(\blk00000003/sig00000837 ),
    .O(\blk00000003/sig000008ab )
  );
  LUT4 #(
    .INIT ( 16'h21DE ))
  \blk00000003/blk00000929  (
    .I0(\blk00000003/sig000007f5 ),
    .I1(\blk00000003/sig00000902 ),
    .I2(\blk00000003/sig0000087a ),
    .I3(\blk00000003/sig00000837 ),
    .O(\blk00000003/sig0000088e )
  );
  LUT3 #(
    .INIT ( 8'h6F ))
  \blk00000003/blk00000928  (
    .I0(\blk00000003/sig00000200 ),
    .I1(\blk00000003/sig000001be ),
    .I2(\blk00000003/sig00000910 ),
    .O(\blk00000003/sig000002db )
  );
  LUT3 #(
    .INIT ( 8'h6F ))
  \blk00000003/blk00000927  (
    .I0(\blk00000003/sig00000284 ),
    .I1(\blk00000003/sig00000309 ),
    .I2(\blk00000003/sig0000090e ),
    .O(\blk00000003/sig000003a2 )
  );
  LUT3 #(
    .INIT ( 8'h6F ))
  \blk00000003/blk00000926  (
    .I0(\blk00000003/sig0000034b ),
    .I1(\blk00000003/sig000003d0 ),
    .I2(\blk00000003/sig0000090c ),
    .O(\blk00000003/sig00000469 )
  );
  LUT3 #(
    .INIT ( 8'h6F ))
  \blk00000003/blk00000925  (
    .I0(\blk00000003/sig00000412 ),
    .I1(\blk00000003/sig00000497 ),
    .I2(\blk00000003/sig0000090a ),
    .O(\blk00000003/sig00000530 )
  );
  LUT3 #(
    .INIT ( 8'h6F ))
  \blk00000003/blk00000924  (
    .I0(\blk00000003/sig000004d9 ),
    .I1(\blk00000003/sig0000055e ),
    .I2(\blk00000003/sig00000908 ),
    .O(\blk00000003/sig000005f7 )
  );
  LUT3 #(
    .INIT ( 8'h6F ))
  \blk00000003/blk00000923  (
    .I0(\blk00000003/sig000005a0 ),
    .I1(\blk00000003/sig00000625 ),
    .I2(\blk00000003/sig00000906 ),
    .O(\blk00000003/sig000006be )
  );
  LUT3 #(
    .INIT ( 8'h6F ))
  \blk00000003/blk00000922  (
    .I0(\blk00000003/sig00000667 ),
    .I1(\blk00000003/sig000006ec ),
    .I2(\blk00000003/sig00000904 ),
    .O(\blk00000003/sig00000785 )
  );
  LUT3 #(
    .INIT ( 8'h6F ))
  \blk00000003/blk00000921  (
    .I0(\blk00000003/sig0000072e ),
    .I1(\blk00000003/sig000007b3 ),
    .I2(\blk00000003/sig00000901 ),
    .O(\blk00000003/sig0000084c )
  );
  LUT3 #(
    .INIT ( 8'h6F ))
  \blk00000003/blk00000920  (
    .I0(\blk00000003/sig000007f5 ),
    .I1(\blk00000003/sig0000087a ),
    .I2(\blk00000003/sig00000902 ),
    .O(\blk00000003/sig000008d3 )
  );
  LUT2 #(
    .INIT ( 4'h6 ))
  \blk00000003/blk0000091f  (
    .I0(\blk00000003/sig000000df ),
    .I1(\blk00000003/sig000000c7 ),
    .O(\blk00000003/sig000000ff )
  );
  LUT4 #(
    .INIT ( 16'h53CA ))
  \blk00000003/blk0000091e  (
    .I0(\blk00000003/sig0000006e ),
    .I1(\blk00000003/sig0000002b ),
    .I2(\blk00000003/sig000000e0 ),
    .I3(\blk00000003/sig000000c8 ),
    .O(\blk00000003/sig0000009d )
  );
  LUT4 #(
    .INIT ( 16'h53CA ))
  \blk00000003/blk0000091d  (
    .I0(\blk00000003/sig0000002b ),
    .I1(\blk00000003/sig0000006e ),
    .I2(\blk00000003/sig000000c8 ),
    .I3(\blk00000003/sig000000e0 ),
    .O(\blk00000003/sig0000005a )
  );
  LUT4 #(
    .INIT ( 16'hAA69 ))
  \blk00000003/blk0000091c  (
    .I0(\blk00000003/sig00000241 ),
    .I1(\blk00000003/sig00000200 ),
    .I2(\blk00000003/sig000001be ),
    .I3(\blk00000003/sig00000910 ),
    .O(\blk00000003/sig000002c4 )
  );
  LUT4 #(
    .INIT ( 16'h21DE ))
  \blk00000003/blk0000091b  (
    .I0(\blk00000003/sig00000281 ),
    .I1(\blk00000003/sig00000910 ),
    .I2(\blk00000003/sig000001be ),
    .I3(\blk00000003/sig00000241 ),
    .O(\blk00000003/sig00000282 )
  );
  LUT4 #(
    .INIT ( 16'hAA69 ))
  \blk00000003/blk0000091a  (
    .I0(\blk00000003/sig000002c6 ),
    .I1(\blk00000003/sig00000284 ),
    .I2(\blk00000003/sig00000309 ),
    .I3(\blk00000003/sig0000090e ),
    .O(\blk00000003/sig0000038b )
  );
  LUT4 #(
    .INIT ( 16'h21DE ))
  \blk00000003/blk00000919  (
    .I0(\blk00000003/sig00000284 ),
    .I1(\blk00000003/sig0000090e ),
    .I2(\blk00000003/sig00000309 ),
    .I3(\blk00000003/sig000002c6 ),
    .O(\blk00000003/sig00000349 )
  );
  LUT4 #(
    .INIT ( 16'hAA69 ))
  \blk00000003/blk00000918  (
    .I0(\blk00000003/sig0000038d ),
    .I1(\blk00000003/sig0000034b ),
    .I2(\blk00000003/sig000003d0 ),
    .I3(\blk00000003/sig0000090c ),
    .O(\blk00000003/sig00000452 )
  );
  LUT4 #(
    .INIT ( 16'h21DE ))
  \blk00000003/blk00000917  (
    .I0(\blk00000003/sig0000034b ),
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
    .I2(\blk00000003/sig000004d9 ),
    .I3(\blk00000003/sig0000055e ),
    .O(\blk00000003/sig00000619 )
  );
  LUT4 #(
    .INIT ( 16'h6A59 ))
  \blk00000003/blk000008df  (
    .I0(\blk00000003/sig00000628 ),
    .I1(\blk00000003/sig00000906 ),
    .I2(\blk00000003/sig000005a0 ),
    .I3(\blk00000003/sig00000625 ),
    .O(\blk00000003/sig000006e0 )
  );
  LUT4 #(
    .INIT ( 16'h6A59 ))
  \blk00000003/blk000008de  (
    .I0(\blk00000003/sig000006ef ),
    .I1(\blk00000003/sig00000904 ),
    .I2(\blk00000003/sig00000667 ),
    .I3(\blk00000003/sig000006ec ),
    .O(\blk00000003/sig000007a7 )
  );
  LUT4 #(
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
