EMDCYY/FFTusingFPGA/code/ipcore_dir/SQB.v

////////////////////////////////////////////////////////////////////////////////
// Copyright (c) 1995-2011 Xilinx, Inc.  All rights reserved.
////////////////////////////////////////////////////////////////////////////////
//   ____  ____
//  /   /\/   /
// /___/  \  /    Vendor: Xilinx
// \   \   \/     Version: O.40d
//  \   \         Application: netgen
//  /   /         Filename: SQB.v
// /___/   /\     Timestamp: Wed Jun 05 09:58:03 2013
// \   \  /  \ 
//  \___\/\___\
//             
// Command	: -intstyle ise -w -sim -ofmt verilog ./tmp/_cg\SQB.ngc ./tmp/_cg\SQB.v 
// Device	: 3s500epq208-4
// Input file	: ./tmp/_cg/SQB.ngc
// Output file	: ./tmp/_cg/SQB.v
// # of Modules	: 1
// Design Name	: SQB
// Xilinx        : c:\Xilinx\13.1\ISE_DS\ISE\
//             
// Purpose:    
//     This verilog netlist is a verification model and uses simulation 
//     primitives which may not represent the true implementation of the 
//     device, however the netlist is functionally correct and should not 
//     be modified. This file cannot be synthesized and should only be used 
//     with supported simulation tools.
//             
// Reference:  
//     Command Line Tools User Guide, Chapter 23 and Synthesis and Simulation Design Guide, Chapter 6
//             
////////////////////////////////////////////////////////////////////////////////

`timescale 1 ns/1 ps

module SQB (
  clk, x_out, x_in
)/* synthesis syn_black_box syn_noprune=1 */;
  input clk;
  output [12 : 0] x_out;
  input [24 : 0] x_in;
  
  // synthesis translate_off
  
  wire \blk00000003/sig000002ba ;
  wire \blk00000003/sig000002b9 ;
  wire \blk00000003/sig000002b8 ;
  wire \blk00000003/sig000002b7 ;
  wire \blk00000003/sig000002b6 ;
  wire \blk00000003/sig000002b5 ;
  wire \blk00000003/sig000002b4 ;
  wire \blk00000003/sig000002b3 ;
  wire \blk00000003/sig000002b2 ;
  wire \blk00000003/sig000002b1 ;
  wire \blk00000003/sig000002b0 ;
  wire \blk00000003/sig000002af ;
  wire \blk00000003/sig000002ae ;
  wire \blk00000003/sig000002ad ;
  wire \blk00000003/sig000002ac ;
  wire \blk00000003/sig000002ab ;
  wire \blk00000003/sig000002aa ;
  wire \blk00000003/sig000002a9 ;
  wire \blk00000003/sig000002a8 ;
  wire \blk00000003/sig000002a7 ;
  wire \blk00000003/sig000002a6 ;
  wire \blk00000003/sig000002a5 ;
  wire \blk00000003/sig000002a4 ;
  wire \blk00000003/sig000002a3 ;
  wire \blk00000003/sig000002a2 ;
  wire \blk00000003/sig000002a1 ;
  wire \blk00000003/sig000002a0 ;
  wire \blk00000003/sig0000029f ;
  wire \blk00000003/sig0000029e ;
  wire \blk00000003/sig0000029d ;
  wire \blk00000003/sig0000029c ;
  wire \blk00000003/sig0000029b ;
  wire \blk00000003/sig0000029a ;
  wire \blk00000003/sig00000299 ;
  wire \blk00000003/sig00000298 ;
  wire \blk00000003/sig00000297 ;
  wire \blk00000003/sig00000296 ;
  wire \blk00000003/sig00000295 ;
  wire \blk00000003/sig00000294 ;
  wire \blk00000003/sig00000293 ;
  wire \blk00000003/sig00000292 ;
  wire \blk00000003/sig00000291 ;
  wire \blk00000003/sig00000290 ;
  wire \blk00000003/sig0000028f ;
  wire \blk00000003/sig0000028e ;
  wire \blk00000003/sig0000028d ;
  wire \blk00000003/sig0000028c ;
  wire \blk00000003/sig0000028b ;
  wire \blk00000003/sig0000028a ;
  wire \blk00000003/sig00000289 ;
  wire \blk00000003/sig00000288 ;
  wire \blk00000003/sig00000287 ;
  wire \blk00000003/sig00000286 ;
  wire \blk00000003/sig00000285 ;
  wire \blk00000003/sig00000284 ;
  wire \blk00000003/sig00000283 ;
  wire \blk00000003/sig00000282 ;
  wire \blk00000003/sig00000281 ;
  wire \blk00000003/sig00000280 ;
  wire \blk00000003/sig0000027f ;
  wire \blk00000003/sig0000027e ;
  wire \blk00000003/sig0000027d ;
  wire \blk00000003/sig0000027c ;
  wire \blk00000003/sig0000027b ;
  wire \blk00000003/sig0000027a ;
  wire \blk00000003/sig00000279 ;
  wire \blk00000003/sig00000278 ;
  wire \blk00000003/sig00000277 ;
  wire \blk00000003/sig00000276 ;
  wire \blk00000003/sig00000275 ;
  wire \blk00000003/sig00000274 ;
  wire \blk00000003/sig00000273 ;
  wire \blk00000003/sig00000272 ;
  wire \blk00000003/sig00000271 ;
  wire \blk00000003/sig00000270 ;
  wire \blk00000003/sig0000026f ;
  wire \blk00000003/sig0000026e ;
  wire \blk00000003/sig0000026d ;
  wire \blk00000003/sig0000026c ;
  wire \blk00000003/sig0000026b ;
  wire \blk00000003/sig0000026a ;
  wire \blk00000003/sig00000269 ;
  wire \blk00000003/sig00000268 ;
  wire \blk00000003/sig00000267 ;
  wire \blk00000003/sig00000266 ;
  wire \blk00000003/sig00000265 ;
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
    .I(\blk00000003/sig00000212 ),
    .O(\blk00000003/sig00000211 )
  );
  INV   \blk00000003/blk00000284  (
    .I(\blk00000003/sig000001d6 ),
    .O(\blk00000003/sig00000242 )
  );
  INV   \blk00000003/blk00000283  (
    .I(\blk00000003/sig000001a6 ),
    .O(\blk00000003/sig000001a5 )
  );
  INV   \blk00000003/blk00000282  (
    .I(\blk00000003/sig00000167 ),
    .O(\blk00000003/sig000001e6 )
  );
  INV   \blk00000003/blk00000281  (
    .I(\blk00000003/sig0000025c ),
    .O(\blk00000003/sig0000025d )
  );
  INV   \blk00000003/blk00000280  (
    .I(\blk00000003/sig00000260 ),
    .O(\blk00000003/sig00000261 )
  );
  INV   \blk00000003/blk0000027f  (
    .I(\blk00000003/sig0000002b ),
    .O(\blk00000003/sig0000027b )
  );
  INV   \blk00000003/blk0000027e  (
    .I(\blk00000003/sig0000028c ),
    .O(\blk00000003/sig0000027f )
  );
  INV   \blk00000003/blk0000027d  (
    .I(\blk00000003/sig00000296 ),
    .O(\blk00000003/sig00000289 )
  );
  INV   \blk00000003/blk0000027c  (
    .I(\blk00000003/sig00000297 ),
    .O(\blk00000003/sig0000028a )
  );
  INV   \blk00000003/blk0000027b  (
    .I(\blk00000003/sig00000298 ),
    .O(\blk00000003/sig0000028b )
  );
  INV   \blk00000003/blk0000027a  (
    .I(\blk00000003/sig0000028d ),
    .O(\blk00000003/sig00000280 )
  );
  INV   \blk00000003/blk00000279  (
    .I(\blk00000003/sig0000028e ),
    .O(\blk00000003/sig00000281 )
  );
  INV   \blk00000003/blk00000278  (
    .I(\blk00000003/sig0000028f ),
    .O(\blk00000003/sig00000282 )
  );
  INV   \blk00000003/blk00000277  (
    .I(\blk00000003/sig00000290 ),
    .O(\blk00000003/sig00000283 )
  );
  INV   \blk00000003/blk00000276  (
    .I(\blk00000003/sig00000291 ),
    .O(\blk00000003/sig00000284 )
  );
  INV   \blk00000003/blk00000275  (
    .I(\blk00000003/sig00000292 ),
    .O(\blk00000003/sig00000285 )
  );
  INV   \blk00000003/blk00000274  (
    .I(\blk00000003/sig00000293 ),
    .O(\blk00000003/sig00000286 )
  );
  INV   \blk00000003/blk00000273  (
    .I(\blk00000003/sig00000294 ),
    .O(\blk00000003/sig00000287 )
  );
  INV   \blk00000003/blk00000272  (
    .I(\blk00000003/sig00000295 ),
    .O(\blk00000003/sig00000288 )
  );
  LUT3 #(
    .INIT ( 8'hA7 ))
  \blk00000003/blk00000271  (
    .I0(\blk00000003/sig000002a5 ),
    .I1(\blk00000003/sig000002a4 ),
    .I2(\blk00000003/sig000002a6 ),
    .O(\blk00000003/sig000000a4 )
  );
  FDR #(
    .INIT ( 1'b0 ))
  \blk00000003/blk00000270  (
    .C(clk),
    .D(\blk00000003/sig00000029 ),
    .R(\blk00000003/sig000002a6 ),
    .Q(\blk00000003/sig00000107 )
  );
  LUT3 #(
    .INIT ( 8'hC2 ))
  \blk00000003/blk0000026f  (
    .I0(\blk00000003/sig000002a5 ),
    .I1(\blk00000003/sig000002a6 ),
    .I2(\blk00000003/sig000002a4 ),
    .O(\blk00000003/sig000000aa )
  );
  LUT3 #(
    .INIT ( 8'hAC ))
  \blk00000003/blk0000026e  (
    .I0(\blk00000003/sig000000b1 ),
    .I1(\blk00000003/sig000000b0 ),
    .I2(\blk00000003/sig0000009e ),
    .O(\blk00000003/sig0000009a )
  );
  LUT3 #(
    .INIT ( 8'hAC ))
  \blk00000003/blk0000026d  (
    .I0(\blk00000003/sig000000ae ),
    .I1(\blk00000003/sig000000ad ),
    .I2(\blk00000003/sig0000009e ),
    .O(\blk00000003/sig00000098 )
  );
  LUT3 #(
    .INIT ( 8'hAC ))
  \blk00000003/blk0000026c  (
    .I0(\blk00000003/sig000000aa ),
    .I1(\blk00000003/sig000000a9 ),
    .I2(\blk00000003/sig0000009e ),
    .O(\blk00000003/sig00000096 )
  );
  LUT3 #(
    .INIT ( 8'hAC ))
  \blk00000003/blk0000026b  (
    .I0(\blk00000003/sig000000a6 ),
    .I1(\blk00000003/sig000000a5 ),
    .I2(\blk00000003/sig0000009e ),
    .O(\blk00000003/sig00000094 )
  );
  LUT3 #(
    .INIT ( 8'hAB ))
  \blk00000003/blk0000026a  (
    .I0(\blk00000003/sig000002a6 ),
    .I1(\blk00000003/sig000002a4 ),
    .I2(\blk00000003/sig000002a5 ),
    .O(\blk00000003/sig0000009c )
  );
  LUT3 #(
    .INIT ( 8'hA8 ))
  \blk00000003/blk00000269  (
    .I0(\blk00000003/sig000002a5 ),
    .I1(\blk00000003/sig000002a4 ),
    .I2(\blk00000003/sig000002a6 ),
    .O(\blk00000003/sig000000a6 )
  );
  LUT3 #(
    .INIT ( 8'hAC ))
  \blk00000003/blk00000268  (
    .I0(\blk00000003/sig00000093 ),
    .I1(\blk00000003/sig00000092 ),
    .I2(\blk00000003/sig0000005a ),
    .O(\blk00000003/sig00000042 )
  );
  LUT3 #(
    .INIT ( 8'hAC ))
  \blk00000003/blk00000267  (
    .I0(\blk00000003/sig0000006c ),
    .I1(\blk00000003/sig0000006b ),
    .I2(\blk00000003/sig0000005a ),
    .O(\blk00000003/sig0000002e )
  );
  LUT3 #(
    .INIT ( 8'hAC ))
  \blk00000003/blk00000266  (
    .I0(\blk00000003/sig00000068 ),
    .I1(\blk00000003/sig00000067 ),
    .I2(\blk00000003/sig0000005a ),
    .O(\blk00000003/sig0000002c )
  );
  LUT3 #(
    .INIT ( 8'hAC ))
  \blk00000003/blk00000265  (
    .I0(\blk00000003/sig00000064 ),
    .I1(\blk00000003/sig00000063 ),
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
    .DI(\blk00000003/sig00000002 ),
    .S(\blk00000003/sig00000029 ),
    .O(\blk00000003/sig0000025f )
  );
  XORCY   \blk00000003/blk0000019f  (
    .CI(\blk00000003/sig0000027a ),
    .LI(\blk00000003/sig0000027b ),
    .O(\NLW_blk00000003/blk0000019f_O_UNCONNECTED )
  );
  MUXCY   \blk00000003/blk0000019e  (
    .CI(\blk00000003/sig0000027a ),
    .DI(\blk00000003/sig0000002b ),
    .S(\blk00000003/sig0000027b ),
    .O(\blk00000003/sig0000027c )
  );
  XORCY   \blk00000003/blk0000019d  (
    .CI(\blk00000003/sig00000278 ),
    .LI(\blk00000003/sig00000279 ),
    .O(\NLW_blk00000003/blk0000019d_O_UNCONNECTED )
  );
  MUXCY   \blk00000003/blk0000019c  (
    .CI(\blk00000003/sig00000278 ),
    .DI(\blk00000003/sig0000002d ),
    .S(\blk00000003/sig00000279 ),
    .O(\blk00000003/sig0000027a )
  );
  XORCY   \blk00000003/blk0000019b  (
    .CI(\blk00000003/sig00000276 ),
    .LI(\blk00000003/sig00000277 ),
    .O(\NLW_blk00000003/blk0000019b_O_UNCONNECTED )
  );
  MUXCY   \blk00000003/blk0000019a  (
    .CI(\blk00000003/sig00000276 ),
    .DI(\blk00000003/sig0000002f ),
    .S(\blk00000003/sig00000277 ),
    .O(\blk00000003/sig00000278 )
  );
  XORCY   \blk00000003/blk00000199  (
    .CI(\blk00000003/sig00000274 ),
    .LI(\blk00000003/sig00000275 ),
    .O(\NLW_blk00000003/blk00000199_O_UNCONNECTED )
  );
  MUXCY   \blk00000003/blk00000198  (
    .CI(\blk00000003/sig00000274 ),
    .DI(\blk00000003/sig00000031 ),
    .S(\blk00000003/sig00000275 ),
    .O(\blk00000003/sig00000276 )
  );
  XORCY   \blk00000003/blk00000197  (
    .CI(\blk00000003/sig00000272 ),
    .LI(\blk00000003/sig00000273 ),
    .O(\NLW_blk00000003/blk00000197_O_UNCONNECTED )
  );
  MUXCY   \blk00000003/blk00000196  (
    .CI(\blk00000003/sig00000272 ),
    .DI(\blk00000003/sig00000033 ),
    .S(\blk00000003/sig00000273 ),
    .O(\blk00000003/sig00000274 )
  );
  XORCY   \blk00000003/blk00000195  (
    .CI(\blk00000003/sig00000270 ),
    .LI(\blk00000003/sig00000271 ),
    .O(\NLW_blk00000003/blk00000195_O_UNCONNECTED )
  );
  MUXCY   \blk00000003/blk00000194  (
    .CI(\blk00000003/sig00000270 ),
    .DI(\blk00000003/sig00000035 ),
    .S(\blk00000003/sig00000271 ),
    .O(\blk00000003/sig00000272 )
  );
  XORCY   \blk00000003/blk00000193  (
    .CI(\blk00000003/sig0000026e ),
    .LI(\blk00000003/sig0000026f ),
    .O(\NLW_blk00000003/blk00000193_O_UNCONNECTED )
  );
  MUXCY   \blk00000003/blk00000192  (
    .CI(\blk00000003/sig0000026e ),
    .DI(\blk00000003/sig00000037 ),
    .S(\blk00000003/sig0000026f ),
    .O(\blk00000003/sig00000270 )
  );
  XORCY   \blk00000003/blk00000191  (
    .CI(\blk00000003/sig0000026c ),
    .LI(\blk00000003/sig0000026d ),
    .O(\NLW_blk00000003/blk00000191_O_UNCONNECTED )
  );
  MUXCY   \blk00000003/blk00000190  (
    .CI(\blk00000003/sig0000026c ),
    .DI(\blk00000003/sig00000039 ),
    .S(\blk00000003/sig0000026d ),
    .O(\blk00000003/sig0000026e )
  );
  XORCY   \blk00000003/blk0000018f  (
    .CI(\blk00000003/sig0000026a ),
    .LI(\blk00000003/sig0000026b ),
    .O(\NLW_blk00000003/blk0000018f_O_UNCONNECTED )
  );
  MUXCY   \blk00000003/blk0000018e  (
    .CI(\blk00000003/sig0000026a ),
    .DI(\blk00000003/sig0000003b ),
    .S(\blk00000003/sig0000026b ),
    .O(\blk00000003/sig0000026c )
  );
  XORCY   \blk00000003/blk0000018d  (
    .CI(\blk00000003/sig00000268 ),
    .LI(\blk00000003/sig00000269 ),
    .O(\NLW_blk00000003/blk0000018d_O_UNCONNECTED )
  );
  MUXCY   \blk00000003/blk0000018c  (
    .CI(\blk00000003/sig00000268 ),
    .DI(\blk00000003/sig0000003d ),
    .S(\blk00000003/sig00000269 ),
    .O(\blk00000003/sig0000026a )
  );
  XORCY   \blk00000003/blk0000018b  (
    .CI(\blk00000003/sig00000266 ),
    .LI(\blk00000003/sig00000267 ),
    .O(\NLW_blk00000003/blk0000018b_O_UNCONNECTED )
  );
  MUXCY   \blk00000003/blk0000018a  (
    .CI(\blk00000003/sig00000266 ),
    .DI(\blk00000003/sig0000003f ),
    .S(\blk00000003/sig00000267 ),
    .O(\blk00000003/sig00000268 )
  );
  XORCY   \blk00000003/blk00000189  (
    .CI(\blk00000003/sig00000264 ),
    .LI(\blk00000003/sig00000265 ),
    .O(\NLW_blk00000003/blk00000189_O_UNCONNECTED )
  );
  MUXCY   \blk00000003/blk00000188  (
    .CI(\blk00000003/sig00000264 ),
    .DI(\blk00000003/sig00000041 ),
    .S(\blk00000003/sig00000265 ),
    .O(\blk00000003/sig00000266 )
  );
  XORCY   \blk00000003/blk00000187  (
    .CI(\blk00000003/sig00000262 ),
    .LI(\blk00000003/sig00000263 ),
    .O(\NLW_blk00000003/blk00000187_O_UNCONNECTED )
  );
  MUXCY   \blk00000003/blk00000186  (
    .CI(\blk00000003/sig00000262 ),
    .DI(\blk00000003/sig00000043 ),
    .S(\blk00000003/sig00000263 ),
    .O(\blk00000003/sig00000264 )
  );
  XORCY   \blk00000003/blk00000185  (
    .CI(\blk00000003/sig0000025e ),
    .LI(\blk00000003/sig00000261 ),
    .O(\NLW_blk00000003/blk00000185_O_UNCONNECTED )
  );
  MUXCY   \blk00000003/blk00000184  (
    .CI(\blk00000003/sig0000025e ),
    .DI(\blk00000003/sig00000260 ),
    .S(\blk00000003/sig00000261 ),
    .O(\blk00000003/sig00000262 )
  );
  XORCY   \blk00000003/blk00000183  (
    .CI(\blk00000003/sig0000025f ),
    .LI(\blk00000003/sig00000029 ),
    .O(\NLW_blk00000003/blk00000183_O_UNCONNECTED )
  );
  XORCY   \blk00000003/blk00000182  (
    .CI(\blk00000003/sig00000002 ),
    .LI(\blk00000003/sig0000025d ),
    .O(\NLW_blk00000003/blk00000182_O_UNCONNECTED )
  );
  MUXCY   \blk00000003/blk00000181  (
    .CI(\blk00000003/sig00000002 ),
    .DI(\blk00000003/sig0000025c ),
    .S(\blk00000003/sig0000025d ),
    .O(\blk00000003/sig0000025e )
  );
  MUXCY   \blk00000003/blk00000180  (
    .CI(\blk00000003/sig00000002 ),
    .DI(\blk00000003/sig0000025b ),
    .S(\blk00000003/sig00000259 ),
    .O(\blk00000003/sig00000255 )
  );
  XORCY   \blk00000003/blk0000017f  (
    .CI(\blk00000003/sig00000002 ),
    .LI(\blk00000003/sig00000259 ),
    .O(\blk00000003/sig0000025a )
  );
  XORCY   \blk00000003/blk0000017e  (
    .CI(\blk00000003/sig00000240 ),
    .LI(\blk00000003/sig00000029 ),
    .O(\NLW_blk00000003/blk0000017e_O_UNCONNECTED )
  );
  MUXCY   \blk00000003/blk0000017d  (
    .CI(\blk00000003/sig00000255 ),
    .DI(\blk00000003/sig00000258 ),
    .S(\blk00000003/sig00000256 ),
    .O(\blk00000003/sig00000252 )
  );
  XORCY   \blk00000003/blk0000017c  (
    .CI(\blk00000003/sig00000255 ),
    .LI(\blk00000003/sig00000256 ),
    .O(\blk00000003/sig00000257 )
  );
  MUXCY   \blk00000003/blk0000017b  (
    .CI(\blk00000003/sig00000252 ),
    .DI(\blk00000003/sig000001e2 ),
    .S(\blk00000003/sig00000253 ),
    .O(\blk00000003/sig0000024f )
  );
  XORCY   \blk00000003/blk0000017a  (
    .CI(\blk00000003/sig00000252 ),
    .LI(\blk00000003/sig00000253 ),
    .O(\blk00000003/sig00000254 )
  );
  MUXCY   \blk00000003/blk00000179  (
    .CI(\blk00000003/sig0000024f ),
    .DI(\blk00000003/sig000001e0 ),
    .S(\blk00000003/sig00000250 ),
    .O(\blk00000003/sig0000024c )
  );
  XORCY   \blk00000003/blk00000178  (
    .CI(\blk00000003/sig0000024f ),
    .LI(\blk00000003/sig00000250 ),
    .O(\blk00000003/sig00000251 )
  );
  MUXCY   \blk00000003/blk00000177  (
    .CI(\blk00000003/sig0000024c ),
    .DI(\blk00000003/sig000001de ),
    .S(\blk00000003/sig0000024d ),
    .O(\blk00000003/sig00000249 )
  );
  XORCY   \blk00000003/blk00000176  (
    .CI(\blk00000003/sig0000024c ),
    .LI(\blk00000003/sig0000024d ),
    .O(\blk00000003/sig0000024e )
  );
  MUXCY   \blk00000003/blk00000175  (
    .CI(\blk00000003/sig00000249 ),
    .DI(\blk00000003/sig000001dc ),
    .S(\blk00000003/sig0000024a ),
    .O(\blk00000003/sig00000246 )
  );
  XORCY   \blk00000003/blk00000174  (
    .CI(\blk00000003/sig00000249 ),
    .LI(\blk00000003/sig0000024a ),
    .O(\blk00000003/sig0000024b )
  );
  MUXCY   \blk00000003/blk00000173  (
    .CI(\blk00000003/sig00000246 ),
    .DI(\blk00000003/sig000001da ),
    .S(\blk00000003/sig00000247 ),
    .O(\blk00000003/sig00000243 )
  );
  XORCY   \blk00000003/blk00000172  (
    .CI(\blk00000003/sig00000246 ),
    .LI(\blk00000003/sig00000247 ),
    .O(\blk00000003/sig00000248 )
  );
  MUXCY   \blk00000003/blk00000171  (
    .CI(\blk00000003/sig00000243 ),
    .DI(\blk00000003/sig000001d8 ),
    .S(\blk00000003/sig00000244 ),
    .O(\blk00000003/sig00000241 )
  );
  XORCY   \blk00000003/blk00000170  (
    .CI(\blk00000003/sig00000243 ),
    .LI(\blk00000003/sig00000244 ),
    .O(\blk00000003/sig00000245 )
  );
  MUXCY   \blk00000003/blk0000016f  (
    .CI(\blk00000003/sig00000241 ),
    .DI(\blk00000003/sig000001d6 ),
    .S(\blk00000003/sig00000242 ),
    .O(\blk00000003/sig0000023f )
  );
  XORCY   \blk00000003/blk0000016e  (
    .CI(\blk00000003/sig00000241 ),
    .LI(\blk00000003/sig00000242 ),
    .O(\NLW_blk00000003/blk0000016e_O_UNCONNECTED )
  );
  MUXCY   \blk00000003/blk0000016d  (
    .CI(\blk00000003/sig0000023f ),
    .DI(\blk00000003/sig00000002 ),
    .S(\blk00000003/sig00000029 ),
    .O(\blk00000003/sig00000240 )
  );
  XORCY   \blk00000003/blk0000016c  (
    .CI(\blk00000003/sig0000023f ),
    .LI(\blk00000003/sig00000029 ),
    .O(\blk00000003/sig00000236 )
  );
  FDRE #(
    .INIT ( 1'b0 ))
  \blk00000003/blk0000016b  (
    .C(clk),
    .CE(\blk00000003/sig00000029 ),
    .D(\blk00000003/sig0000023e ),
    .R(\blk00000003/sig00000002 ),
    .Q(\blk00000003/sig0000022e )
  );
  FDRE #(
    .INIT ( 1'b0 ))
  \blk00000003/blk0000016a  (
    .C(clk),
    .CE(\blk00000003/sig00000029 ),
    .D(\blk00000003/sig0000023d ),
    .R(\blk00000003/sig00000002 ),
    .Q(\blk00000003/sig0000022a )
  );
  FDRE #(
    .INIT ( 1'b0 ))
  \blk00000003/blk00000169  (
    .C(clk),
    .CE(\blk00000003/sig00000029 ),
    .D(\blk00000003/sig0000023c ),
    .R(\blk00000003/sig00000002 ),
    .Q(\blk00000003/sig00000226 )
  );
  FDRE #(
    .INIT ( 1'b0 ))
  \blk00000003/blk00000168  (
    .C(clk),
    .CE(\blk00000003/sig00000029 ),
    .D(\blk00000003/sig0000023b ),
    .R(\blk00000003/sig00000002 ),
    .Q(\blk00000003/sig00000222 )
  );
  FDRE #(
    .INIT ( 1'b0 ))
  \blk00000003/blk00000167  (
    .C(clk),
    .CE(\blk00000003/sig00000029 ),
    .D(\blk00000003/sig0000023a ),
    .R(\blk00000003/sig00000002 ),
    .Q(\blk00000003/sig0000021e )
  );
  FDRE #(
    .INIT ( 1'b0 ))
  \blk00000003/blk00000166  (
    .C(clk),
    .CE(\blk00000003/sig00000029 ),
    .D(\blk00000003/sig00000239 ),
    .R(\blk00000003/sig00000002 ),
    .Q(\blk00000003/sig0000021a )
  );
  FDRE #(
    .INIT ( 1'b0 ))
  \blk00000003/blk00000165  (
    .C(clk),
    .CE(\blk00000003/sig00000029 ),
    .D(\blk00000003/sig00000238 ),
    .R(\blk00000003/sig00000002 ),
    .Q(\blk00000003/sig00000216 )
  );
  FDRE #(
    .INIT ( 1'b0 ))
  \blk00000003/blk00000164  (
    .C(clk),
    .CE(\blk00000003/sig00000029 ),
    .D(\blk00000003/sig00000237 ),
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
    .Q(\blk00000003/sig000001aa )
  );
  FDRE #(
    .INIT ( 1'b0 ))
  \blk00000003/blk0000013d  (
    .C(clk),
    .CE(\blk00000003/sig00000029 ),
    .D(\blk00000003/sig00000205 ),
    .R(\blk00000003/sig00000002 ),
    .Q(\blk00000003/sig000001a6 )
  );
  FDRE #(
    .INIT ( 1'b0 ))
  \blk00000003/blk0000013c  (
    .C(clk),
    .CE(\blk00000003/sig00000029 ),
    .D(\blk00000003/sig00000204 ),
    .R(\blk00000003/sig00000002 ),
    .Q(\blk00000003/sig00000196 )
  );
  FDRE #(
    .INIT ( 1'b0 ))
  \blk00000003/blk0000013b  (
    .C(clk),
    .CE(\blk00000003/sig00000029 ),
    .D(\blk00000003/sig00000203 ),
    .R(\blk00000003/sig00000002 ),
    .Q(\blk00000003/sig00000195 )
  );
  FDRE #(
    .INIT ( 1'b0 ))
  \blk00000003/blk0000013a  (
    .C(clk),
    .CE(\blk00000003/sig00000029 ),
    .D(\blk00000003/sig00000202 ),
    .R(\blk00000003/sig00000002 ),
    .Q(\blk00000003/sig00000194 )
  );
  FDRE #(
    .INIT ( 1'b0 ))
  \blk00000003/blk00000139  (
    .C(clk),
    .CE(\blk00000003/sig00000029 ),
    .D(\blk00000003/sig00000201 ),
    .R(\blk00000003/sig00000002 ),
    .Q(\blk00000003/sig00000193 )
  );
  FDRE #(
    .INIT ( 1'b0 ))
  \blk00000003/blk00000138  (
    .C(clk),
    .CE(\blk00000003/sig00000029 ),
    .D(\blk00000003/sig00000200 ),
    .R(\blk00000003/sig00000002 ),
    .Q(\blk00000003/sig00000192 )
  );
  FDRE #(
    .INIT ( 1'b0 ))
  \blk00000003/blk00000137  (
    .C(clk),
    .CE(\blk00000003/sig00000029 ),
    .D(\blk00000003/sig000001ff ),
    .R(\blk00000003/sig00000002 ),
    .Q(\blk00000003/sig00000191 )
  );
  FDRE #(
    .INIT ( 1'b0 ))
  \blk00000003/blk00000136  (
    .C(clk),
    .CE(\blk00000003/sig00000029 ),
    .D(\blk00000003/sig000001fe ),
    .R(\blk00000003/sig00000002 ),
    .Q(\blk00000003/sig00000190 )
  );
  FDRE #(
    .INIT ( 1'b0 ))
  \blk00000003/blk00000135  (
    .C(clk),
    .CE(\blk00000003/sig00000029 ),
    .D(\blk00000003/sig000001fd ),
    .R(\blk00000003/sig00000002 ),
    .Q(\blk00000003/sig0000018f )
  );
  MUXCY   \blk00000003/blk00000134  (
    .CI(\blk00000003/sig00000002 ),
    .DI(\blk00000003/sig000001fc ),
    .S(\blk00000003/sig000001fa ),
    .O(\blk00000003/sig000001f6 )
  );
  XORCY   \blk00000003/blk00000133  (
    .CI(\blk00000003/sig00000002 ),
    .LI(\blk00000003/sig000001fa ),
    .O(\blk00000003/sig000001fb )
  );
  XORCY   \blk00000003/blk00000132  (
    .CI(\blk00000003/sig000001e4 ),
    .LI(\blk00000003/sig00000029 ),
    .O(\NLW_blk00000003/blk00000132_O_UNCONNECTED )
  );
  MUXCY   \blk00000003/blk00000131  (
    .CI(\blk00000003/sig000001f6 ),
    .DI(\blk00000003/sig000001f9 ),
    .S(\blk00000003/sig000001f7 ),
    .O(\blk00000003/sig000001f3 )
  );
  XORCY   \blk00000003/blk00000130  (
    .CI(\blk00000003/sig000001f6 ),
    .LI(\blk00000003/sig000001f7 ),
    .O(\blk00000003/sig000001f8 )
  );
  MUXCY   \blk00000003/blk0000012f  (
    .CI(\blk00000003/sig000001f3 ),
    .DI(\blk00000003/sig00000171 ),
    .S(\blk00000003/sig000001f4 ),
    .O(\blk00000003/sig000001f0 )
  );
  XORCY   \blk00000003/blk0000012e  (
    .CI(\blk00000003/sig000001f3 ),
    .LI(\blk00000003/sig000001f4 ),
    .O(\blk00000003/sig000001f5 )
  );
  MUXCY   \blk00000003/blk0000012d  (
    .CI(\blk00000003/sig000001f0 ),
    .DI(\blk00000003/sig0000016f ),
    .S(\blk00000003/sig000001f1 ),
    .O(\blk00000003/sig000001ed )
  );
  XORCY   \blk00000003/blk0000012c  (
    .CI(\blk00000003/sig000001f0 ),
    .LI(\blk00000003/sig000001f1 ),
    .O(\blk00000003/sig000001f2 )
  );
  MUXCY   \blk00000003/blk0000012b  (
    .CI(\blk00000003/sig000001ed ),
    .DI(\blk00000003/sig0000016d ),
    .S(\blk00000003/sig000001ee ),
    .O(\blk00000003/sig000001ea )
  );
  XORCY   \blk00000003/blk0000012a  (
    .CI(\blk00000003/sig000001ed ),
    .LI(\blk00000003/sig000001ee ),
    .O(\blk00000003/sig000001ef )
  );
  MUXCY   \blk00000003/blk00000129  (
    .CI(\blk00000003/sig000001ea ),
    .DI(\blk00000003/sig0000016b ),
    .S(\blk00000003/sig000001eb ),
    .O(\blk00000003/sig000001e7 )
  );
  XORCY   \blk00000003/blk00000128  (
    .CI(\blk00000003/sig000001ea ),
    .LI(\blk00000003/sig000001eb ),
    .O(\blk00000003/sig000001ec )
  );
  MUXCY   \blk00000003/blk00000127  (
    .CI(\blk00000003/sig000001e7 ),
    .DI(\blk00000003/sig00000169 ),
    .S(\blk00000003/sig000001e8 ),
    .O(\blk00000003/sig000001e5 )
  );
  XORCY   \blk00000003/blk00000126  (
    .CI(\blk00000003/sig000001e7 ),
    .LI(\blk00000003/sig000001e8 ),
    .O(\blk00000003/sig000001e9 )
  );
  MUXCY   \blk00000003/blk00000125  (
    .CI(\blk00000003/sig000001e5 ),
    .DI(\blk00000003/sig00000167 ),
    .S(\blk00000003/sig000001e6 ),
    .O(\blk00000003/sig000001e3 )
  );
  XORCY   \blk00000003/blk00000124  (
    .CI(\blk00000003/sig000001e5 ),
    .LI(\blk00000003/sig000001e6 ),
    .O(\NLW_blk00000003/blk00000124_O_UNCONNECTED )
  );
  MUXCY   \blk00000003/blk00000123  (
    .CI(\blk00000003/sig000001e3 ),
    .DI(\blk00000003/sig00000002 ),
    .S(\blk00000003/sig00000029 ),
    .O(\blk00000003/sig000001e4 )
  );
  XORCY   \blk00000003/blk00000122  (
    .CI(\blk00000003/sig000001e3 ),
    .LI(\blk00000003/sig00000029 ),
    .O(\blk00000003/sig000001d3 )
  );
  FDRE #(
    .INIT ( 1'b0 ))
  \blk00000003/blk00000121  (
    .C(clk),
    .CE(\blk00000003/sig00000029 ),
    .D(\blk00000003/sig000001e1 ),
    .R(\blk00000003/sig00000002 ),
    .Q(\blk00000003/sig000001e2 )
  );
  FDRE #(
    .INIT ( 1'b0 ))
  \blk00000003/blk00000120  (
    .C(clk),
    .CE(\blk00000003/sig00000029 ),
    .D(\blk00000003/sig000001df ),
    .R(\blk00000003/sig00000002 ),
    .Q(\blk00000003/sig000001e0 )
  );
  FDRE #(
    .INIT ( 1'b0 ))
  \blk00000003/blk0000011f  (
    .C(clk),
    .CE(\blk00000003/sig00000029 ),
    .D(\blk00000003/sig000001dd ),
    .R(\blk00000003/sig00000002 ),
    .Q(\blk00000003/sig000001de )
  );
  FDRE #(
    .INIT ( 1'b0 ))
  \blk00000003/blk0000011e  (
    .C(clk),
    .CE(\blk00000003/sig00000029 ),
    .D(\blk00000003/sig000001db ),
    .R(\blk00000003/sig00000002 ),
    .Q(\blk00000003/sig000001dc )
  );
  FDRE #(
    .INIT ( 1'b0 ))
  \blk00000003/blk0000011d  (
    .C(clk),
    .CE(\blk00000003/sig00000029 ),
    .D(\blk00000003/sig000001d9 ),
    .R(\blk00000003/sig00000002 ),
    .Q(\blk00000003/sig000001da )
  );
  FDRE #(
    .INIT ( 1'b0 ))
  \blk00000003/blk0000011c  (
    .C(clk),
    .CE(\blk00000003/sig00000029 ),
    .D(\blk00000003/sig000001d7 ),
    .R(\blk00000003/sig00000002 ),
    .Q(\blk00000003/sig000001d8 )
  );
  FDRE #(
    .INIT ( 1'b0 ))
  \blk00000003/blk0000011b  (
    .C(clk),
    .CE(\blk00000003/sig00000029 ),
    .D(\blk00000003/sig000001d5 ),
    .R(\blk00000003/sig00000002 ),
    .Q(\blk00000003/sig000001d6 )
  );
  FDRE #(
    .INIT ( 1'b0 ))
  \blk00000003/blk0000011a  (
    .C(clk),
    .CE(\blk00000003/sig00000029 ),
    .D(\blk00000003/sig000001d3 ),
    .R(\blk00000003/sig00000002 ),
    .Q(\blk00000003/sig000001d4 )
  );
  FDRE #(
    .INIT ( 1'b0 ))
  \blk00000003/blk00000119  (
    .C(clk),
    .CE(\blk00000003/sig00000029 ),
    .D(\blk00000003/sig00000177 ),
    .R(\blk00000003/sig00000002 ),
    .Q(\blk00000003/sig000001d2 )
  );
  FDRE #(
    .INIT ( 1'b0 ))
  \blk00000003/blk00000118  (
    .C(clk),
    .CE(\blk00000003/sig00000029 ),
    .D(\blk00000003/sig00000175 ),
    .R(\blk00000003/sig00000002 ),
    .Q(\blk00000003/sig000001d1 )
  );
  FDRE #(
    .INIT ( 1'b0 ))
  \blk00000003/blk00000117  (
    .C(clk),
    .CE(\blk00000003/sig00000029 ),
    .D(\blk00000003/sig00000174 ),
    .R(\blk00000003/sig00000002 ),
    .Q(\blk00000003/sig000001d0 )
  );
  FDRE #(
    .INIT ( 1'b0 ))
  \blk00000003/blk00000116  (
    .C(clk),
    .CE(\blk00000003/sig00000029 ),
    .D(\blk00000003/sig00000173 ),
    .R(\blk00000003/sig00000002 ),
    .Q(\blk00000003/sig000001cf )
  );
  FDRE #(
    .INIT ( 1'b0 ))
  \blk00000003/blk00000115  (
    .C(clk),
    .CE(\blk00000003/sig00000029 ),
    .D(\blk00000003/sig00000172 ),
    .R(\blk00000003/sig00000002 ),
    .Q(\blk00000003/sig000001ce )
  );
  MUXCY   \blk00000003/blk00000114  (
    .CI(\blk00000003/sig00000002 ),
    .DI(\blk00000003/sig000001cd ),
    .S(\blk00000003/sig000001cb ),
    .O(\blk00000003/sig000001c7 )
  );
  XORCY   \blk00000003/blk00000113  (
    .CI(\blk00000003/sig00000002 ),
    .LI(\blk00000003/sig000001cb ),
    .O(\blk00000003/sig000001cc )
  );
  XORCY   \blk00000003/blk00000112  (
    .CI(\blk00000003/sig000001a3 ),
    .LI(\blk00000003/sig00000029 ),
    .O(\NLW_blk00000003/blk00000112_O_UNCONNECTED )
  );
  MUXCY   \blk00000003/blk00000111  (
    .CI(\blk00000003/sig000001c7 ),
    .DI(\blk00000003/sig000001ca ),
    .S(\blk00000003/sig000001c8 ),
    .O(\blk00000003/sig000001c3 )
  );
  XORCY   \blk00000003/blk00000110  (
    .CI(\blk00000003/sig000001c7 ),
    .LI(\blk00000003/sig000001c8 ),
    .O(\blk00000003/sig000001c9 )
  );
  MUXCY   \blk00000003/blk0000010f  (
    .CI(\blk00000003/sig000001c3 ),
    .DI(\blk00000003/sig000001c6 ),
    .S(\blk00000003/sig000001c4 ),
    .O(\blk00000003/sig000001bf )
  );
  XORCY   \blk00000003/blk0000010e  (
    .CI(\blk00000003/sig000001c3 ),
    .LI(\blk00000003/sig000001c4 ),
    .O(\blk00000003/sig000001c5 )
  );
  MUXCY   \blk00000003/blk0000010d  (
    .CI(\blk00000003/sig000001bf ),
    .DI(\blk00000003/sig000001c2 ),
    .S(\blk00000003/sig000001c0 ),
    .O(\blk00000003/sig000001bb )
  );
  XORCY   \blk00000003/blk0000010c  (
    .CI(\blk00000003/sig000001bf ),
    .LI(\blk00000003/sig000001c0 ),
    .O(\blk00000003/sig000001c1 )
  );
  MUXCY   \blk00000003/blk0000010b  (
    .CI(\blk00000003/sig000001bb ),
    .DI(\blk00000003/sig000001be ),
    .S(\blk00000003/sig000001bc ),
    .O(\blk00000003/sig000001b7 )
  );
  XORCY   \blk00000003/blk0000010a  (
    .CI(\blk00000003/sig000001bb ),
    .LI(\blk00000003/sig000001bc ),
    .O(\blk00000003/sig000001bd )
  );
  MUXCY   \blk00000003/blk00000109  (
    .CI(\blk00000003/sig000001b7 ),
    .DI(\blk00000003/sig000001ba ),
    .S(\blk00000003/sig000001b8 ),
    .O(\blk00000003/sig000001b3 )
  );
  XORCY   \blk00000003/blk00000108  (
    .CI(\blk00000003/sig000001b7 ),
    .LI(\blk00000003/sig000001b8 ),
    .O(\blk00000003/sig000001b9 )
  );
  MUXCY   \blk00000003/blk00000107  (
    .CI(\blk00000003/sig000001b3 ),
    .DI(\blk00000003/sig000001b6 ),
    .S(\blk00000003/sig000001b4 ),
    .O(\blk00000003/sig000001af )
  );
  XORCY   \blk00000003/blk00000106  (
    .CI(\blk00000003/sig000001b3 ),
    .LI(\blk00000003/sig000001b4 ),
    .O(\blk00000003/sig000001b5 )
  );
  MUXCY   \blk00000003/blk00000105  (
    .CI(\blk00000003/sig000001af ),
    .DI(\blk00000003/sig000001b2 ),
    .S(\blk00000003/sig000001b0 ),
    .O(\blk00000003/sig000001ab )
  );
  XORCY   \blk00000003/blk00000104  (
    .CI(\blk00000003/sig000001af ),
    .LI(\blk00000003/sig000001b0 ),
    .O(\blk00000003/sig000001b1 )
  );
  MUXCY   \blk00000003/blk00000103  (
    .CI(\blk00000003/sig000001ab ),
    .DI(\blk00000003/sig000001ae ),
    .S(\blk00000003/sig000001ac ),
    .O(\blk00000003/sig000001a7 )
  );
  XORCY   \blk00000003/blk00000102  (
    .CI(\blk00000003/sig000001ab ),
    .LI(\blk00000003/sig000001ac ),
    .O(\blk00000003/sig000001ad )
  );
  MUXCY   \blk00000003/blk00000101  (
    .CI(\blk00000003/sig000001a7 ),
    .DI(\blk00000003/sig000001aa ),
    .S(\blk00000003/sig000001a8 ),
    .O(\blk00000003/sig000001a4 )
  );
  XORCY   \blk00000003/blk00000100  (
    .CI(\blk00000003/sig000001a7 ),
    .LI(\blk00000003/sig000001a8 ),
    .O(\blk00000003/sig000001a9 )
  );
  MUXCY   \blk00000003/blk000000ff  (
    .CI(\blk00000003/sig000001a4 ),
    .DI(\blk00000003/sig000001a6 ),
    .S(\blk00000003/sig000001a5 ),
    .O(\blk00000003/sig000001a2 )
  );
  XORCY   \blk00000003/blk000000fe  (
    .CI(\blk00000003/sig000001a4 ),
    .LI(\blk00000003/sig000001a5 ),
    .O(\NLW_blk00000003/blk000000fe_O_UNCONNECTED )
  );
  MUXCY   \blk00000003/blk000000fd  (
    .CI(\blk00000003/sig000001a2 ),
    .DI(\blk00000003/sig00000002 ),
    .S(\blk00000003/sig00000029 ),
    .O(\blk00000003/sig000001a3 )
  );
  XORCY   \blk00000003/blk000000fc  (
    .CI(\blk00000003/sig000001a2 ),
    .LI(\blk00000003/sig00000029 ),
    .O(\blk00000003/sig00000197 )
  );
  FDRE #(
    .INIT ( 1'b0 ))
  \blk00000003/blk000000fb  (
    .C(clk),
    .CE(\blk00000003/sig00000029 ),
    .D(\blk00000003/sig000001a1 ),
    .R(\blk00000003/sig00000002 ),
    .Q(\blk00000003/sig0000015e )
  );
  FDRE #(
    .INIT ( 1'b0 ))
  \blk00000003/blk000000fa  (
    .C(clk),
    .CE(\blk00000003/sig00000029 ),
    .D(\blk00000003/sig000001a0 ),
    .R(\blk00000003/sig00000002 ),
    .Q(\blk00000003/sig0000015a )
  );
  FDRE #(
    .INIT ( 1'b0 ))
  \blk00000003/blk000000f9  (
    .C(clk),
    .CE(\blk00000003/sig00000029 ),
    .D(\blk00000003/sig0000019f ),
    .R(\blk00000003/sig00000002 ),
    .Q(\blk00000003/sig00000156 )
  );
  FDRE #(
    .INIT ( 1'b0 ))
  \blk00000003/blk000000f8  (
    .C(clk),
    .CE(\blk00000003/sig00000029 ),
    .D(\blk00000003/sig0000019e ),
    .R(\blk00000003/sig00000002 ),
    .Q(\blk00000003/sig00000152 )
  );
  FDRE #(
    .INIT ( 1'b0 ))
  \blk00000003/blk000000f7  (
    .C(clk),
    .CE(\blk00000003/sig00000029 ),
    .D(\blk00000003/sig0000019d ),
    .R(\blk00000003/sig00000002 ),
    .Q(\blk00000003/sig0000014e )
  );
  FDRE #(
    .INIT ( 1'b0 ))
  \blk00000003/blk000000f6  (
    .C(clk),
    .CE(\blk00000003/sig00000029 ),
    .D(\blk00000003/sig0000019c ),
    .R(\blk00000003/sig00000002 ),
    .Q(\blk00000003/sig0000014a )
  );
  FDRE #(
    .INIT ( 1'b0 ))
  \blk00000003/blk000000f5  (
    .C(clk),
    .CE(\blk00000003/sig00000029 ),
    .D(\blk00000003/sig0000019b ),
    .R(\blk00000003/sig00000002 ),
    .Q(\blk00000003/sig00000146 )
  );
  FDRE #(
    .INIT ( 1'b0 ))
  \blk00000003/blk000000f4  (
    .C(clk),
    .CE(\blk00000003/sig00000029 ),
    .D(\blk00000003/sig0000019a ),
    .R(\blk00000003/sig00000002 ),
    .Q(\blk00000003/sig00000142 )
  );
  FDRE #(
    .INIT ( 1'b0 ))
  \blk00000003/blk000000f3  (
    .C(clk),
    .CE(\blk00000003/sig00000029 ),
    .D(\blk00000003/sig00000199 ),
    .R(\blk00000003/sig00000002 ),
    .Q(\blk00000003/sig0000013e )
  );
  FDRE #(
    .INIT ( 1'b0 ))
  \blk00000003/blk000000f2  (
    .C(clk),
    .CE(\blk00000003/sig00000029 ),
    .D(\blk00000003/sig00000198 ),
    .R(\blk00000003/sig00000002 ),
    .Q(\blk00000003/sig0000013a )
  );
  FDRE #(
    .INIT ( 1'b0 ))
  \blk00000003/blk000000f1  (
    .C(clk),
    .CE(\blk00000003/sig00000029 ),
    .D(\blk00000003/sig00000197 ),
    .R(\blk00000003/sig00000002 ),
    .Q(\blk00000003/sig00000129 )
  );
  FDRE #(
    .INIT ( 1'b0 ))
  \blk00000003/blk000000f0  (
    .C(clk),
    .CE(\blk00000003/sig00000029 ),
    .D(\blk00000003/sig00000196 ),
    .R(\blk00000003/sig00000002 ),
    .Q(\blk00000003/sig00000128 )
  );
  FDRE #(
    .INIT ( 1'b0 ))
  \blk00000003/blk000000ef  (
    .C(clk),
    .CE(\blk00000003/sig00000029 ),
    .D(\blk00000003/sig00000195 ),
    .R(\blk00000003/sig00000002 ),
    .Q(\blk00000003/sig00000127 )
  );
  FDRE #(
    .INIT ( 1'b0 ))
  \blk00000003/blk000000ee  (
    .C(clk),
    .CE(\blk00000003/sig00000029 ),
    .D(\blk00000003/sig00000194 ),
    .R(\blk00000003/sig00000002 ),
    .Q(\blk00000003/sig00000126 )
  );
  FDRE #(
    .INIT ( 1'b0 ))
  \blk00000003/blk000000ed  (
    .C(clk),
    .CE(\blk00000003/sig00000029 ),
    .D(\blk00000003/sig00000193 ),
    .R(\blk00000003/sig00000002 ),
    .Q(\blk00000003/sig00000125 )
  );
  FDRE #(
    .INIT ( 1'b0 ))
  \blk00000003/blk000000ec  (
    .C(clk),
    .CE(\blk00000003/sig00000029 ),
    .D(\blk00000003/sig00000192 ),
    .R(\blk00000003/sig00000002 ),
    .Q(\blk00000003/sig00000124 )
  );
  FDRE #(
    .INIT ( 1'b0 ))
  \blk00000003/blk000000eb  (
    .C(clk),
    .CE(\blk00000003/sig00000029 ),
    .D(\blk00000003/sig00000191 ),
    .R(\blk00000003/sig00000002 ),
    .Q(\blk00000003/sig00000123 )
  );
  FDRE #(
    .INIT ( 1'b0 ))
  \blk00000003/blk000000ea  (
    .C(clk),
    .CE(\blk00000003/sig00000029 ),
    .D(\blk00000003/sig00000190 ),
    .R(\blk00000003/sig00000002 ),
    .Q(\blk00000003/sig00000122 )
  );
  FDRE #(
    .INIT ( 1'b0 ))
  \blk00000003/blk000000e9  (
    .C(clk),
    .CE(\blk00000003/sig00000029 ),
    .D(\blk00000003/sig0000018f ),
    .R(\blk00000003/sig00000002 ),
    .Q(\blk00000003/sig00000121 )
  );
  MUXCY   \blk00000003/blk000000e8  (
    .CI(\blk00000003/sig00000002 ),
    .DI(\blk00000003/sig0000018e ),
    .S(\blk00000003/sig0000018c ),
    .O(\blk00000003/sig00000188 )
  );
  XORCY   \blk00000003/blk000000e7  (
    .CI(\blk00000003/sig00000002 ),
    .LI(\blk00000003/sig0000018c ),
    .O(\blk00000003/sig0000018d )
  );
  XORCY   \blk00000003/blk000000e6  (
    .CI(\blk00000003/sig00000179 ),
    .LI(\blk00000003/sig00000029 ),
    .O(\NLW_blk00000003/blk000000e6_O_UNCONNECTED )
  );
  MUXCY   \blk00000003/blk000000e5  (
    .CI(\blk00000003/sig00000188 ),
    .DI(\blk00000003/sig0000018b ),
    .S(\blk00000003/sig00000189 ),
    .O(\blk00000003/sig00000185 )
  );
  XORCY   \blk00000003/blk000000e4  (
    .CI(\blk00000003/sig00000188 ),
    .LI(\blk00000003/sig00000189 ),
    .O(\blk00000003/sig0000018a )
  );
  MUXCY   \blk00000003/blk000000e3  (
    .CI(\blk00000003/sig00000185 ),
    .DI(\blk00000003/sig00000106 ),
    .S(\blk00000003/sig00000186 ),
    .O(\blk00000003/sig00000182 )
  );
  XORCY   \blk00000003/blk000000e2  (
    .CI(\blk00000003/sig00000185 ),
    .LI(\blk00000003/sig00000186 ),
    .O(\blk00000003/sig00000187 )
  );
  MUXCY   \blk00000003/blk000000e1  (
    .CI(\blk00000003/sig00000182 ),
    .DI(\blk00000003/sig00000104 ),
    .S(\blk00000003/sig00000183 ),
    .O(\blk00000003/sig0000017f )
  );
  XORCY   \blk00000003/blk000000e0  (
    .CI(\blk00000003/sig00000182 ),
    .LI(\blk00000003/sig00000183 ),
    .O(\blk00000003/sig00000184 )
  );
  MUXCY   \blk00000003/blk000000df  (
    .CI(\blk00000003/sig0000017f ),
    .DI(\blk00000003/sig00000102 ),
    .S(\blk00000003/sig00000180 ),
    .O(\blk00000003/sig0000017c )
  );
  XORCY   \blk00000003/blk000000de  (
    .CI(\blk00000003/sig0000017f ),
    .LI(\blk00000003/sig00000180 ),
    .O(\blk00000003/sig00000181 )
  );
  MUXCY   \blk00000003/blk000000dd  (
    .CI(\blk00000003/sig0000017c ),
    .DI(\blk00000003/sig00000100 ),
    .S(\blk00000003/sig0000017d ),
    .O(\blk00000003/sig0000017a )
  );
  XORCY   \blk00000003/blk000000dc  (
    .CI(\blk00000003/sig0000017c ),
    .LI(\blk00000003/sig0000017d ),
    .O(\blk00000003/sig0000017e )
  );
  MUXCY   \blk00000003/blk000000db  (
    .CI(\blk00000003/sig0000017a ),
    .DI(\blk00000003/sig000000fe ),
    .S(\blk00000003/sig0000017b ),
    .O(\blk00000003/sig00000178 )
  );
  XORCY   \blk00000003/blk000000da  (
    .CI(\blk00000003/sig0000017a ),
    .LI(\blk00000003/sig0000017b ),
    .O(\NLW_blk00000003/blk000000da_O_UNCONNECTED )
  );
  MUXCY   \blk00000003/blk000000d9  (
    .CI(\blk00000003/sig00000178 ),
    .DI(\blk00000003/sig00000002 ),
    .S(\blk00000003/sig00000029 ),
    .O(\blk00000003/sig00000179 )
  );
  XORCY   \blk00000003/blk000000d8  (
    .CI(\blk00000003/sig00000178 ),
    .LI(\blk00000003/sig00000029 ),
    .O(\blk00000003/sig00000176 )
  );
  FDRE #(
    .INIT ( 1'b0 ))
  \blk00000003/blk000000d7  (
    .C(clk),
    .CE(\blk00000003/sig00000029 ),
    .D(\blk00000003/sig00000176 ),
    .R(\blk00000003/sig00000002 ),
    .Q(\blk00000003/sig00000177 )
  );
  FDRE #(
    .INIT ( 1'b0 ))
  \blk00000003/blk000000d6  (
    .C(clk),
    .CE(\blk00000003/sig00000029 ),
    .D(\blk00000003/sig0000010c ),
    .R(\blk00000003/sig00000002 ),
    .Q(\blk00000003/sig00000175 )
  );
  FDRE #(
    .INIT ( 1'b0 ))
  \blk00000003/blk000000d5  (
    .C(clk),
    .CE(\blk00000003/sig00000029 ),
    .D(\blk00000003/sig0000010a ),
    .R(\blk00000003/sig00000002 ),
    .Q(\blk00000003/sig00000174 )
  );
  FDRE #(
    .INIT ( 1'b0 ))
  \blk00000003/blk000000d4  (
    .C(clk),
    .CE(\blk00000003/sig00000029 ),
    .D(\blk00000003/sig00000109 ),
    .R(\blk00000003/sig00000002 ),
    .Q(\blk00000003/sig00000173 )
  );
  FDRE #(
    .INIT ( 1'b0 ))
  \blk00000003/blk000000d3  (
    .C(clk),
    .CE(\blk00000003/sig00000029 ),
    .D(\blk00000003/sig00000108 ),
    .R(\blk00000003/sig00000002 ),
    .Q(\blk00000003/sig00000172 )
  );
  FDRE #(
    .INIT ( 1'b0 ))
  \blk00000003/blk000000d2  (
    .C(clk),
    .CE(\blk00000003/sig00000029 ),
    .D(\blk00000003/sig00000170 ),
    .R(\blk00000003/sig00000002 ),
    .Q(\blk00000003/sig00000171 )
  );
  FDRE #(
    .INIT ( 1'b0 ))
  \blk00000003/blk000000d1  (
    .C(clk),
    .CE(\blk00000003/sig00000029 ),
    .D(\blk00000003/sig0000016e ),
    .R(\blk00000003/sig00000002 ),
    .Q(\blk00000003/sig0000016f )
  );
  FDRE #(
    .INIT ( 1'b0 ))
  \blk00000003/blk000000d0  (
    .C(clk),
    .CE(\blk00000003/sig00000029 ),
    .D(\blk00000003/sig0000016c ),
    .R(\blk00000003/sig00000002 ),
    .Q(\blk00000003/sig0000016d )
  );
  FDRE #(
    .INIT ( 1'b0 ))
  \blk00000003/blk000000cf  (
    .C(clk),
    .CE(\blk00000003/sig00000029 ),
    .D(\blk00000003/sig0000016a ),
    .R(\blk00000003/sig00000002 ),
    .Q(\blk00000003/sig0000016b )
  );
  FDRE #(
    .INIT ( 1'b0 ))
  \blk00000003/blk000000ce  (
    .C(clk),
    .CE(\blk00000003/sig00000029 ),
    .D(\blk00000003/sig00000168 ),
    .R(\blk00000003/sig00000002 ),
    .Q(\blk00000003/sig00000169 )
  );
  FDRE #(
    .INIT ( 1'b0 ))
  \blk00000003/blk000000cd  (
    .C(clk),
    .CE(\blk00000003/sig00000029 ),
    .D(\blk00000003/sig00000166 ),
    .R(\blk00000003/sig00000002 ),
    .Q(\blk00000003/sig00000167 )
  );
  MUXCY   \blk00000003/blk000000cc  (
    .CI(\blk00000003/sig00000002 ),
    .DI(\blk00000003/sig00000165 ),
    .S(\blk00000003/sig00000163 ),
    .O(\blk00000003/sig0000015f )
  );
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
