EMDCYY/FFTusingFPGA/code/LCD.vhd

library IEEE;
use IEEE.STD_LOGIC_1164.ALL;
use IEEE.STD_LOGIC_ARITH.ALL;
use IEEE.STD_LOGIC_SIGNED.ALL;

entity LCD is  --force clk 0 0 ,1 10000 -r 20000
port(  
       OE      : out std_logic;
       DIR1    : out std_logic;
       DIR2    : out std_logic;
       LCD_EN  : out std_logic;
       LCD_RS  : out std_logic := '0';
       LCD_RW  : out std_logic;
       LCD_DATA: out std_logic_vector(7 downto 0);
		  clk    :  in std_logic;
		 phase   :  in std_logic_vector(25 downto 0) := "11100110110011000111000000"
     );
end LCD;

architecture Behavioral of LCD is
component transfer
	port (
	clk: in std_logic;
	sclr: in std_logic;
	rfd: out std_logic;
	dividend: in std_logic_vector(25 downto 0);
	divisor: in std_logic_vector(25 downto 0);
	quotient: out std_logic_vector(25 downto 0);
	fractional: out std_logic_vector(25 downto 0));
end component;

type   DAT_STATES is (dat_str,dat_hdrs,dat_tens,dat_unit,dat_punit,dat_ptens,dat_phdrs);
signal dat_state: DAT_STATES := dat_str;

signal   dividend: std_logic_vector(25 downto 0) := "00000000000000000000000000";
signal    divisor: std_logic_vector(25 downto 0) := "00000000000000000000000000" ;
signal   quotient: std_logic_vector(25 downto 0) := "00000000000000000000000000";
signal fractional: std_logic_vector(25 downto 0) := "00000000000000000000000000";

signal phase_abs: std_logic_vector(25 downto 0) := "00000000000000000000000000";
signal       cnt: integer range 0 to 255:= 0;
signal      sclr: std_logic := '0';
signal       rfd: std_logic := '0';

signal CNT_LCDCLK :INTEGER RANGE 0 TO 250000;
signal LCD_CLK : std_logic :='1';
type   LCD_STATES is (set_function,clear_display,set_cursor,set_display,set_ddram1,write_data1,set_ddram2,write_data2);
signal lcd_state: LCD_STATES := set_function;

signal sign  : std_logic_vector (7 downto 0):="00000000"; 
signal hdrs  : std_logic_vector (7 downto 0):="00000000"; 
signal tens  : std_logic_vector (7 downto 0):="00000000"; 
signal unit  : std_logic_vector (7 downto 0):="00000000"; 
signal ptens : std_logic_vector (7 downto 0):="00000000"; 
signal punit : std_logic_vector (7 downto 0):="00000000";
signal phdrs : std_logic_vector (7 downto 0):="00000000"; 
type ram is array (0 to 15) of std_logic_vector (7 downto 0);
--	 constant ram1 : ram:=(x"44",x"44",x"53",x"20",x"46",x"52",x"45",x"51",x"3A",x"31",x"30",x"2e",x"30",x"4b",x"48",x"7a"); --DDS FREQ:10.0KHz
constant ram1 : ram:=(x"20",x"50",x"68",x"61",x"73",x"65",x"20",x"45",x"72",x"72",x"6f",x"72",x"20",x"3a",x"20",x"20");     --_Phase_Error_:__  
constant ram2 : ram:=(x"20",x"20",x"20", sign, hdrs, tens, unit,x"2e",punit,ptens,phdrs,x"df",x"20",x"20",x"20",x"20");     --___?XXX.XXX?____

BEGIN
INST_HDRS : TRANSFER
  port map (
			clk => clk,
			rfd => rfd,
			sclr=> sclr,
			dividend => dividend,         --width 26
			divisor =>   divisor,         --      26
			quotient => quotient,         --      26
			fractional => fractional      --      26 
			);
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
