EMDCYY/FFTusingFPGA/code/DCM.vhd

--------------------------------------------------------------------------------
-- Copyright (c) 1995-2011 Xilinx, Inc.  All rights reserved.
--------------------------------------------------------------------------------
--   ____  ____ 
--  /   /\/   / 
-- /___/  \  /    Vendor: Xilinx 
-- \   \   \/     Version : 13.1
--  \   \         Application : xaw2vhdl
--  /   /         Filename : DCM.vhd
-- /___/   /\     Timestamp : 05/31/2013 10:44:13
-- \   \  /  \ 
--  \___\/\___\ 
--
--Command: xaw2vhdl-intstyle E:/Design of Laser Tracer/8.ADM/ADMDSP_VHDL/AMH/ipcore_dir/DCM.xaw -st DCM.vhd
--Design Name: DCM
--Device: xc3s500e-4pq208
--
-- Module DCM
-- Generated by Xilinx Architecture Wizard
-- Written for synthesis tool: XST
-- Period Jitter (unit interval) for block DCM_SP_INST = 0.09 UI
-- Period Jitter (Peak-to-Peak) for block DCM_SP_INST = 1.34 ns

library ieee;
use ieee.std_logic_1164.ALL;
use ieee.numeric_std.ALL;
library UNISIM;
use UNISIM.Vcomponents.ALL;

entity DCM is
   port ( CLKIN_IN        : in    std_logic; 
          CLKFX_OUT       : out   std_logic; 
          CLKIN_IBUFG_OUT : out   std_logic; 
          CLK0_OUT        : out   std_logic; 
          CLK180_OUT      : out   std_logic; 
          LOCKED_OUT      : out   std_logic);
end DCM;
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
